lassiipk/ModuPad_v2/Assets/nice!view/Screenshot 2026-01-20 105709.png

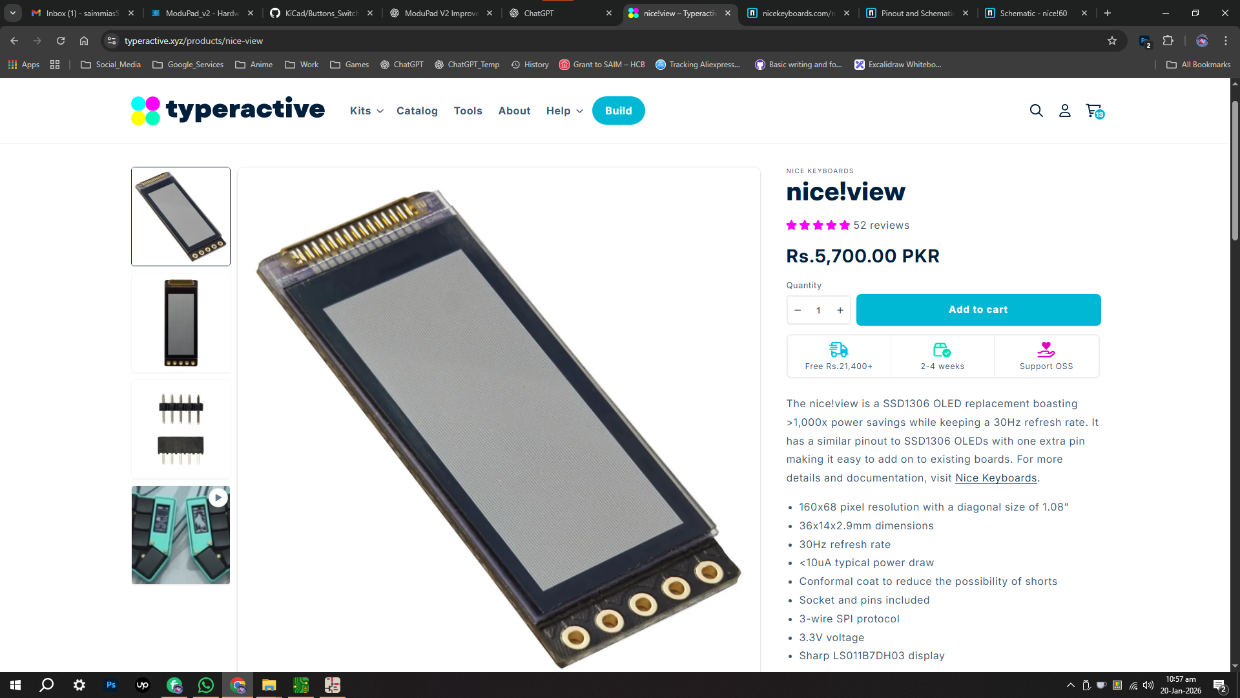
Assets/nice!view/Screenshot 2026-01-20 105709.png
