lassiipk/ModuPad_v2/CAD/Knobs/Knurled Encoder Knob/Knob Back.png

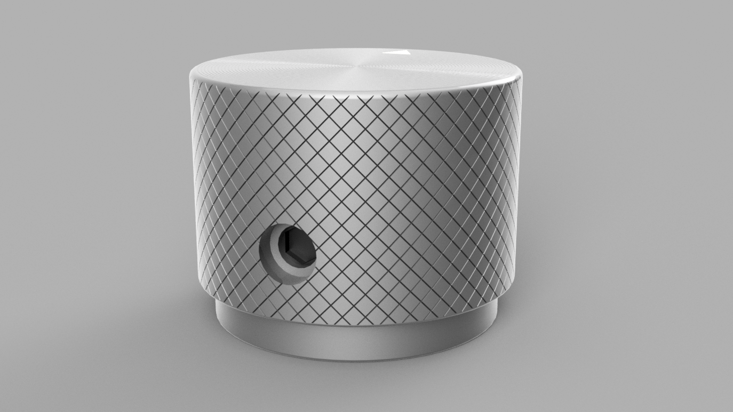
CAD/Knobs/Knurled Encoder Knob/Knob Back.png
