lassiipk/ModuPad_v2/CAD/Knobs/Knurled Encoder Knob/Knob Bottom.png

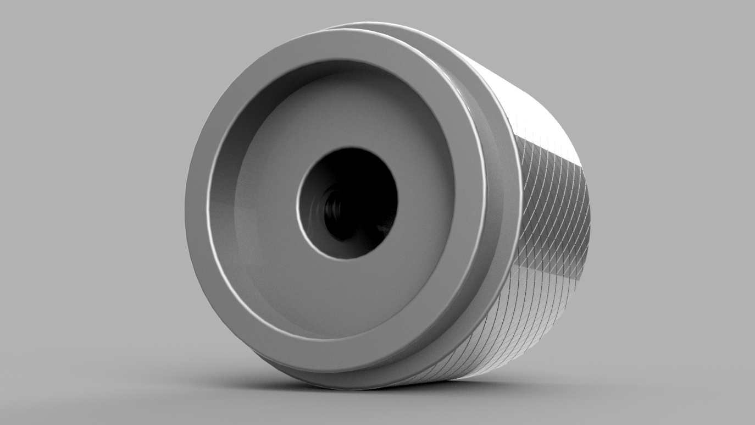
CAD/Knobs/Knurled Encoder Knob/Knob Bottom.png
