lassiipk/ModuPad_v2/CAD/Knobs/Knurled Encoder Knob/Knob Top.png

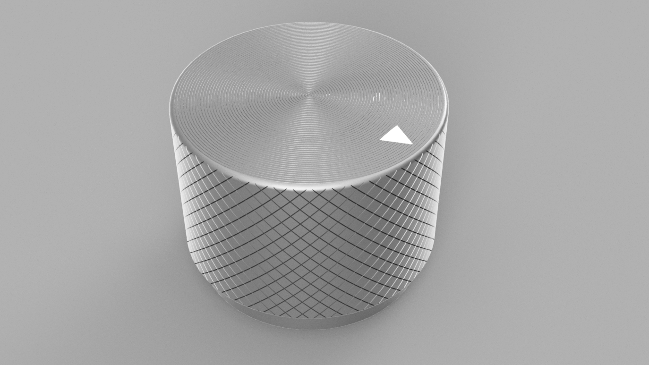
CAD/Knobs/Knurled Encoder Knob/Knob Top.png
