lassiipk/ModuPad_v2/Images/CAD/CAD_Sketch/CAD_Bottom_Sketch_Screenshot 2026-01-29 163341.png

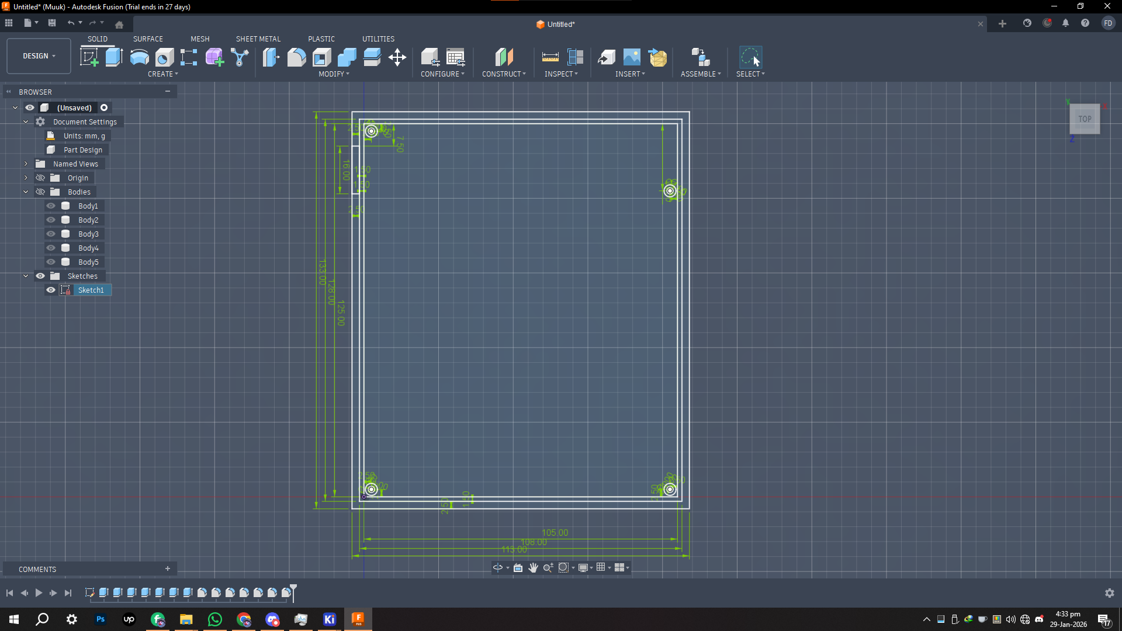
Images/CAD/CAD_Sketch/CAD_Bottom_Sketch_Screenshot 2026-01-29 163341.png
