lassiipk/ModuPad_v2/Images/CAD/CAD_Sketch/Screenshot 2026-01-31 225652.png

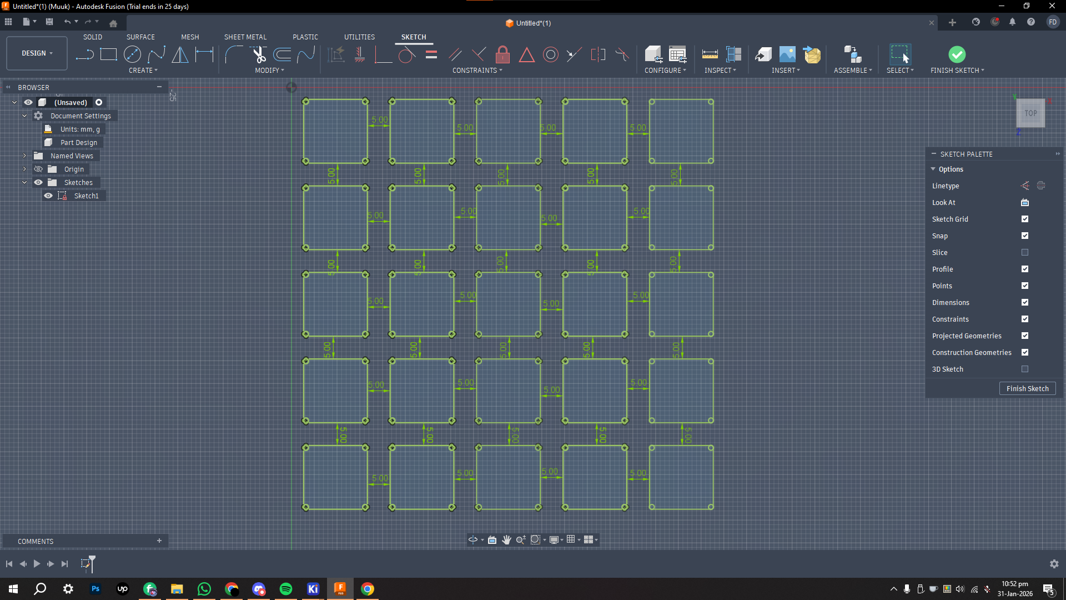
Images/CAD/CAD_Sketch/Screenshot 2026-01-31 225652.png
