lassiipk/ModuPad_v2/Images/CAD/CAD_Sketch/Screenshot 2026-01-31 235744.png

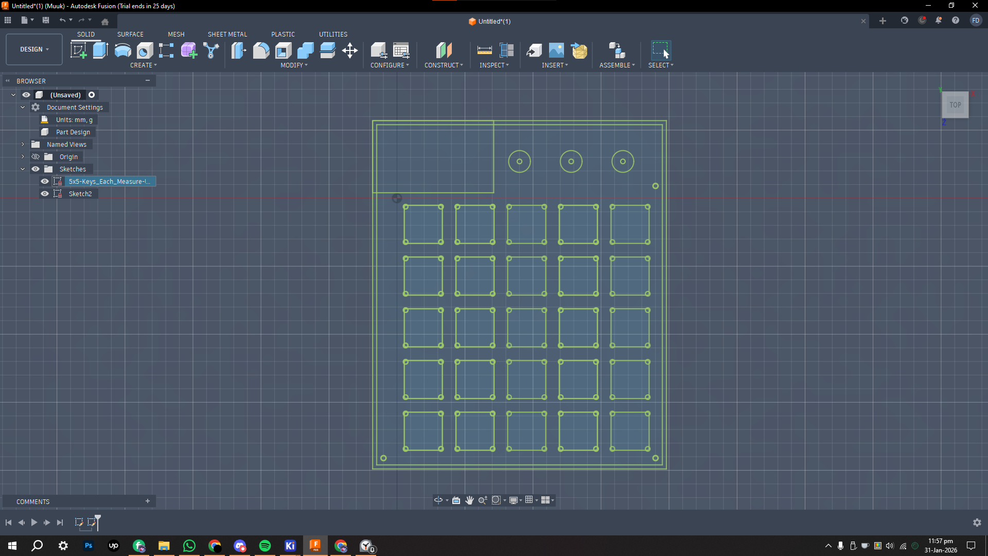
Images/CAD/CAD_Sketch/Screenshot 2026-01-31 235744.png
