lassiipk/ModuPad_v2/Images/CAD/CAD_Sketch/Screenshot 2026-02-04 113914.png

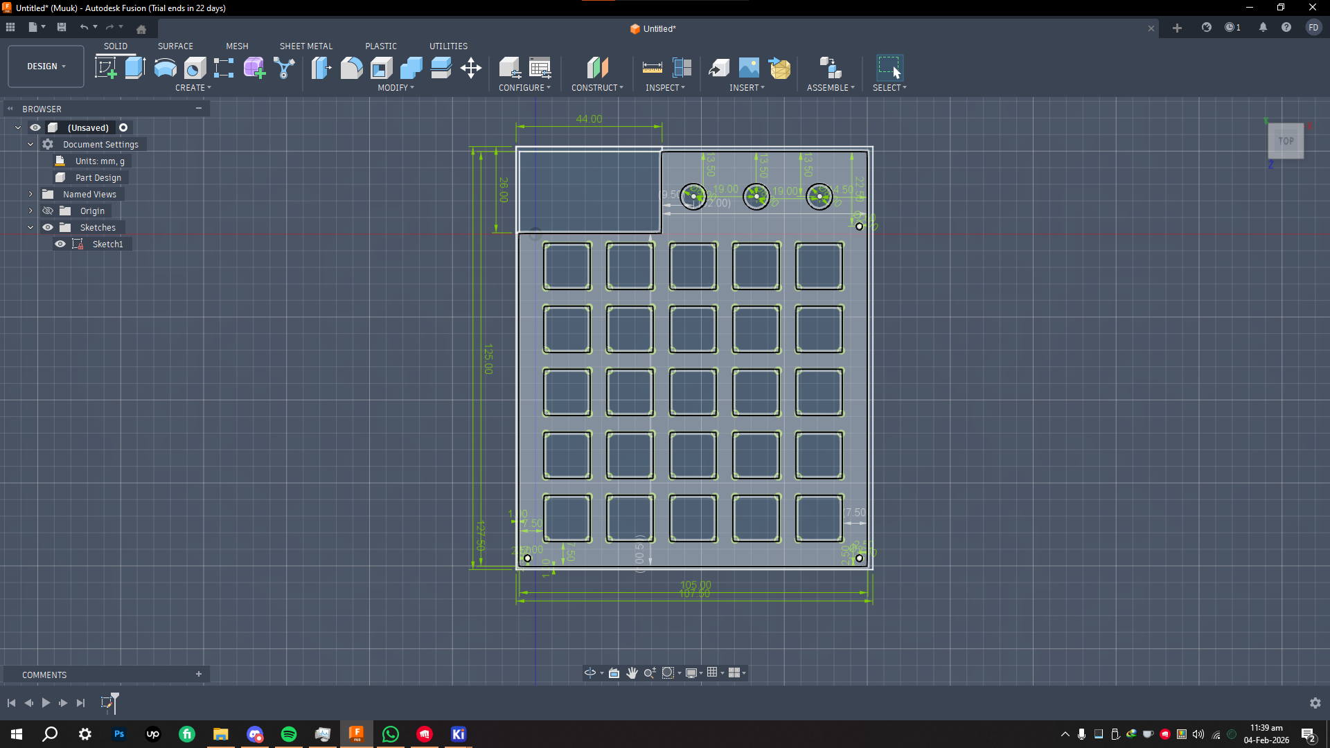
Images/CAD/CAD_Sketch/Screenshot 2026-02-04 113914.png
