lassiipk/ModuPad_v2/Images/CAD/CAD_Solid/CAD_Bottom_Solid_2.o_Screenshot 2026-01-29 163546.png

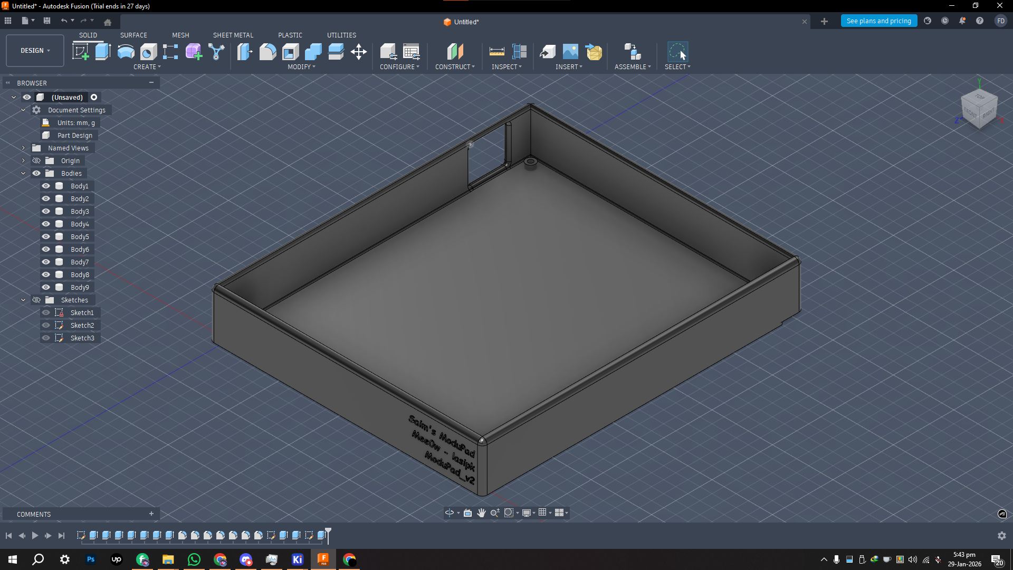
Images/CAD/CAD_Solid/CAD_Bottom_Solid_2.o_Screenshot 2026-01-29 163546.png
