lassiipk/ModuPad_v2/Images/PCB/Screenshot 2026-01-23 115402.png

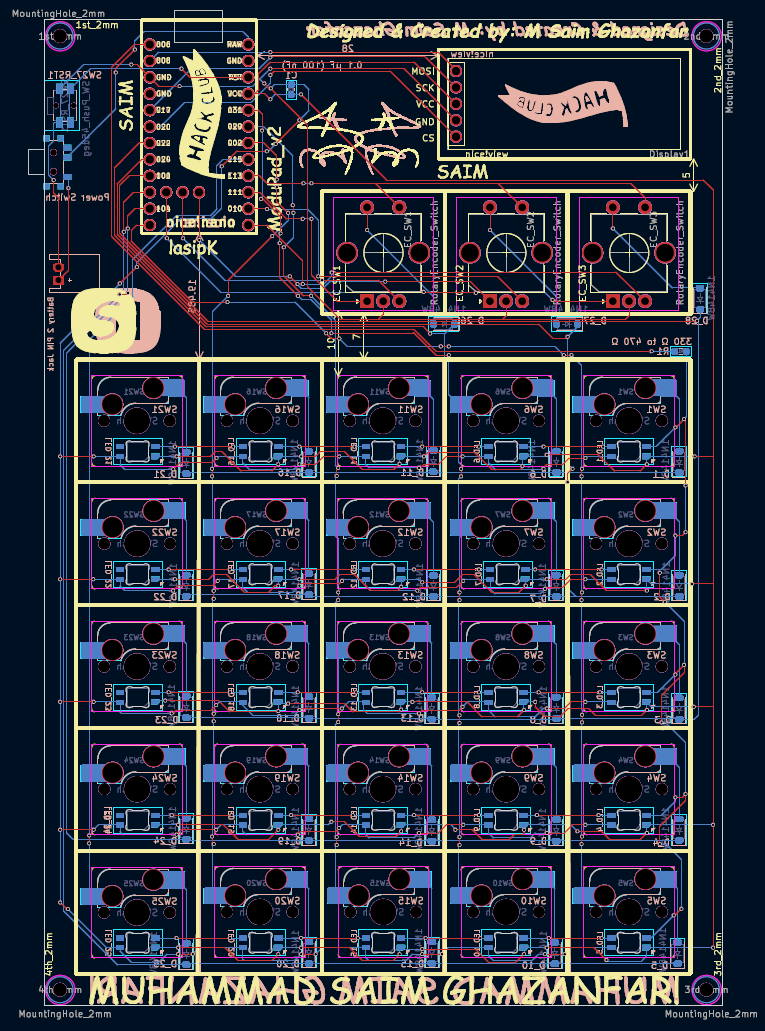
Images/PCB/Screenshot 2026-01-23 115402.png
