lassiipk/ModuPad_v2/Images/PCB/Screenshot 2026-01-26 182227.png

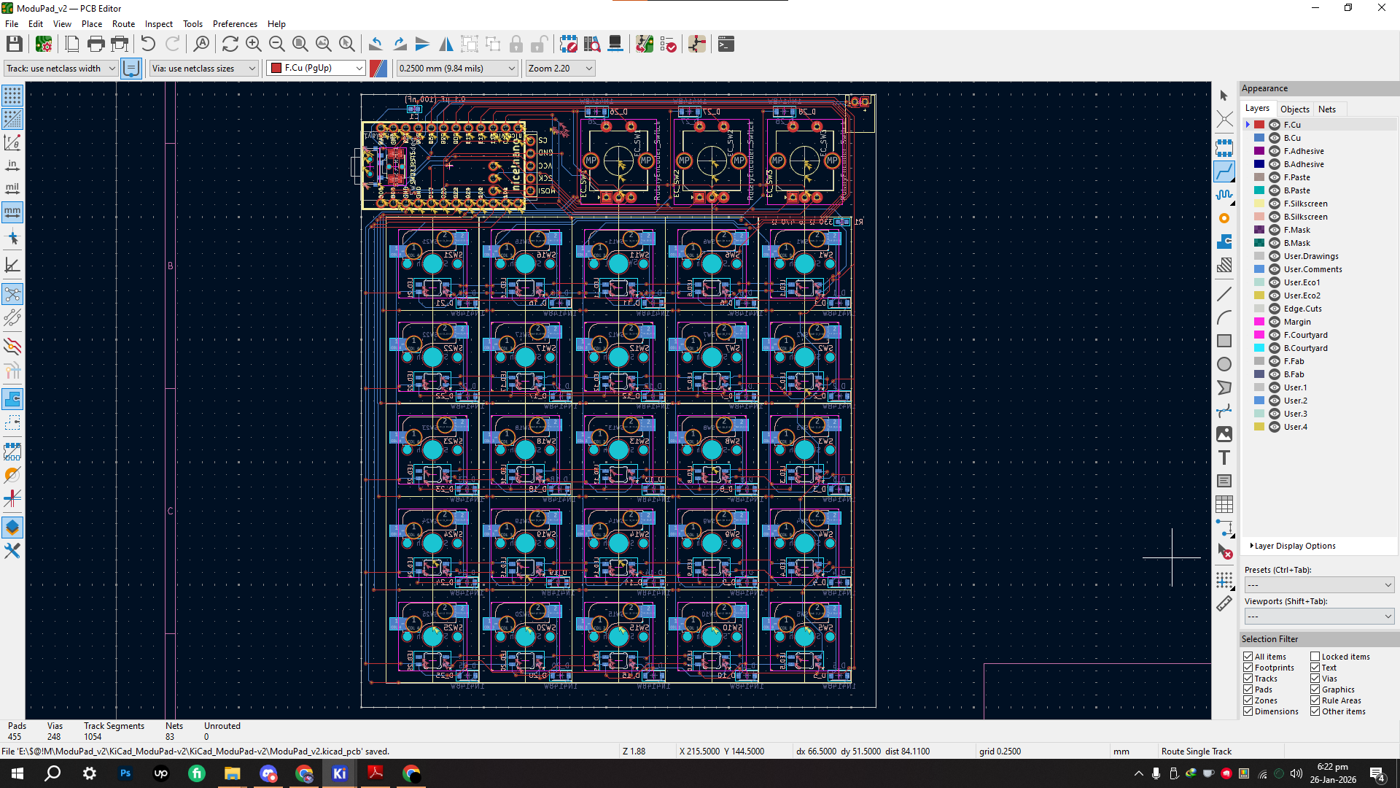
Images/PCB/Screenshot 2026-01-26 182227.png
