lassiipk/ModuPad_v2/Images/PCB/Screenshot 2026-01-27 120922.png

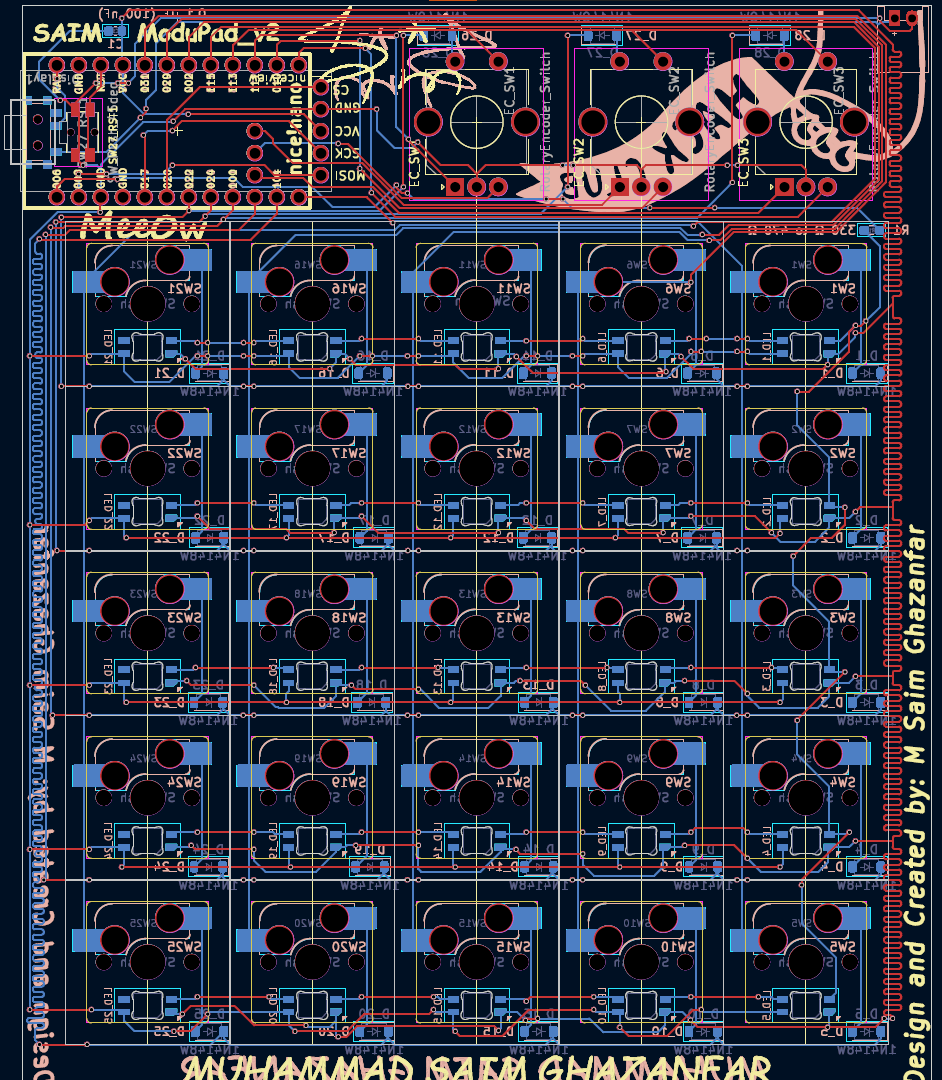
Images/PCB/Screenshot 2026-01-27 120922.png
