lassiipk/ModuPad_v2/Images/PCB/Screenshot 2026-03-08 180335.png

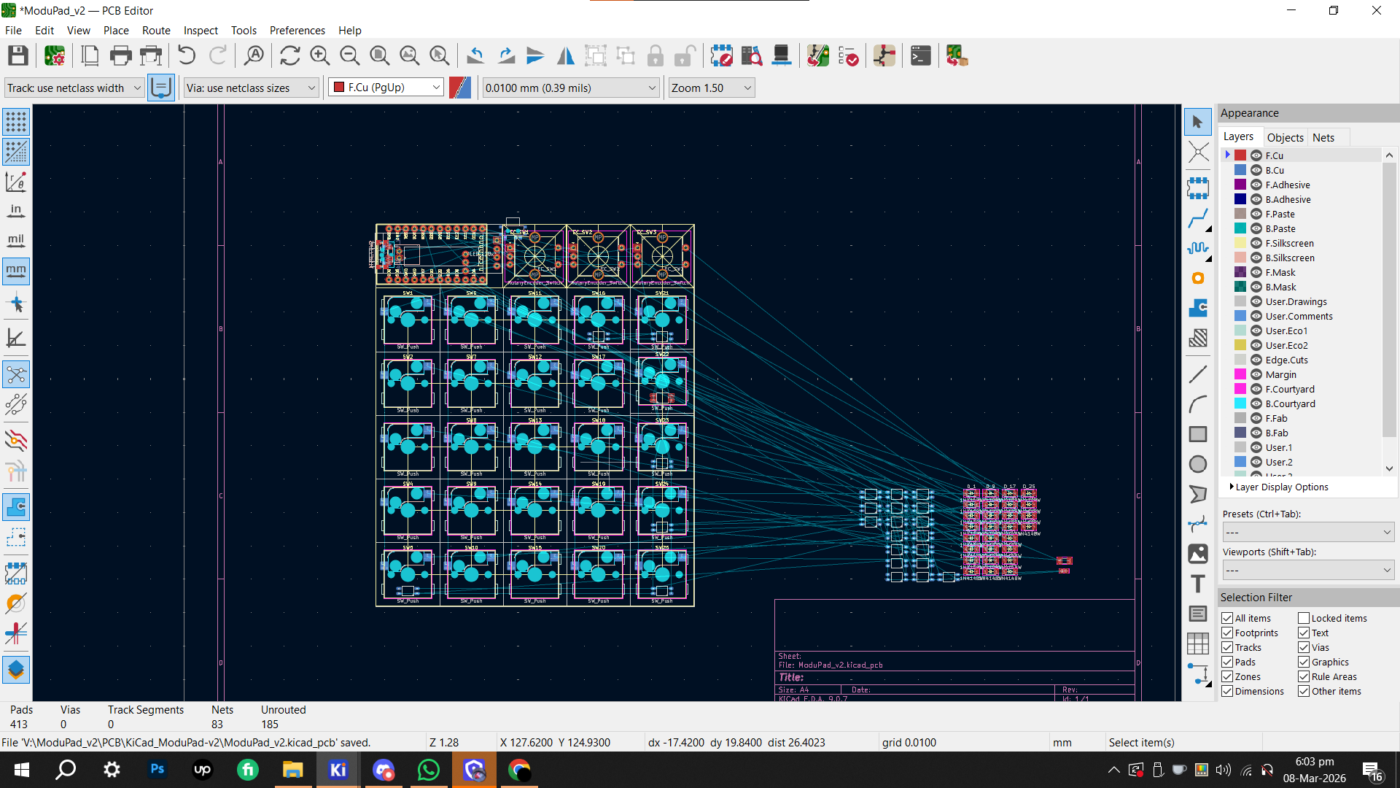
Images/PCB/Screenshot 2026-03-08 180335.png
