lassiipk/ModuPad_v2/Images/PCB/Screenshot 2026-03-09 xxxxxx.png

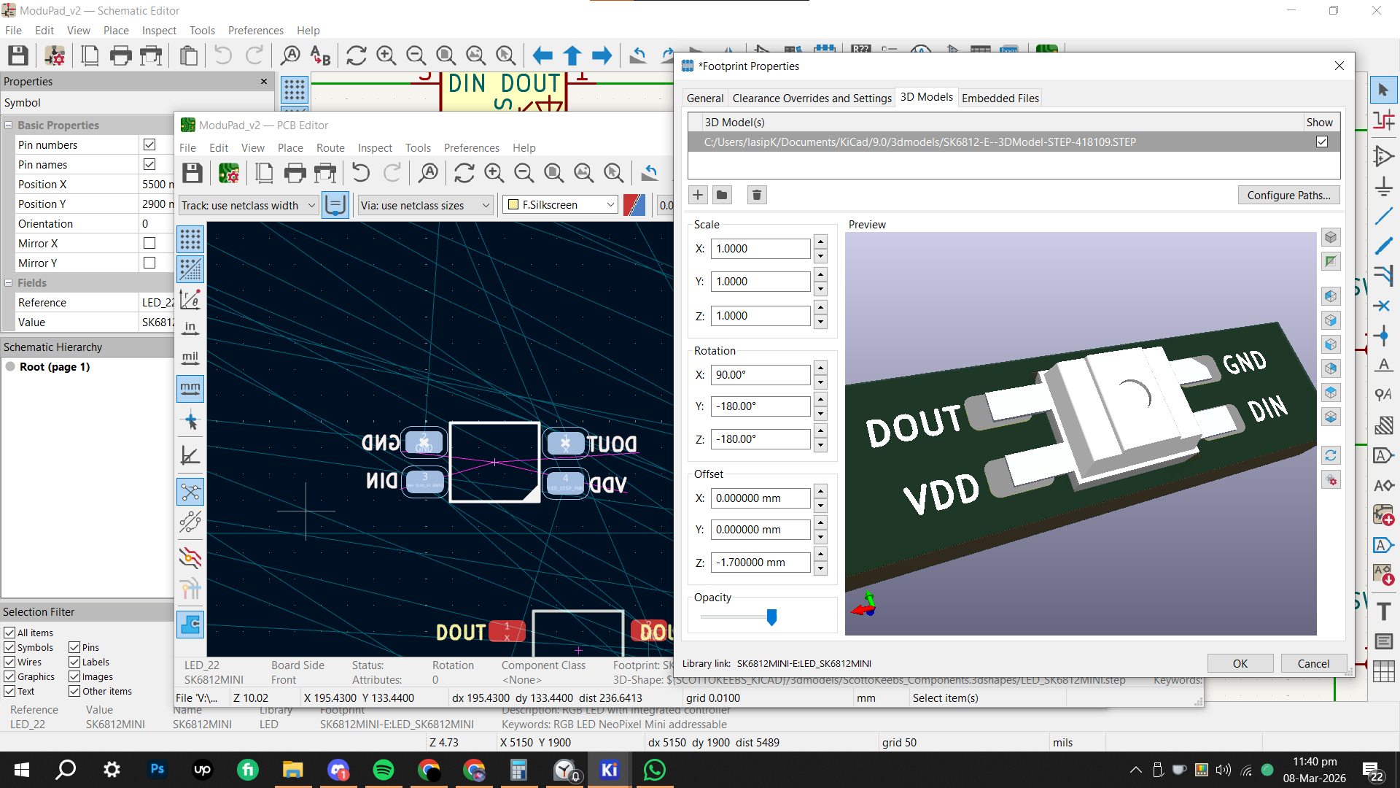
Images/PCB/Screenshot 2026-03-09 xxxxxx.png
