lassiipk/ModuPad_v2/Images/PCB/Screenshot 2026-03-10 152446.png

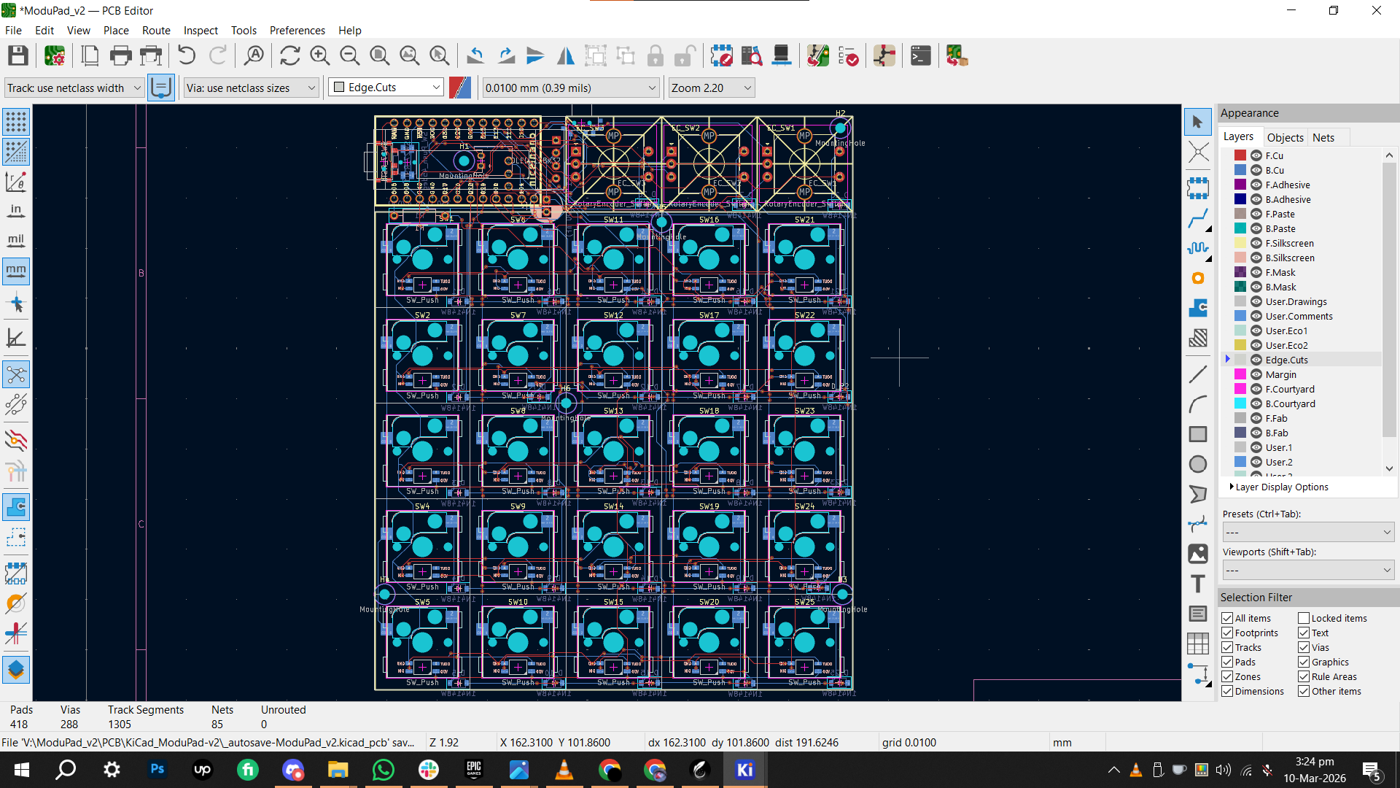
Images/PCB/Screenshot 2026-03-10 152446.png
