lassiipk/ModuPad_v2/Images/PCB/Screenshot 2026-03-20 000157.png

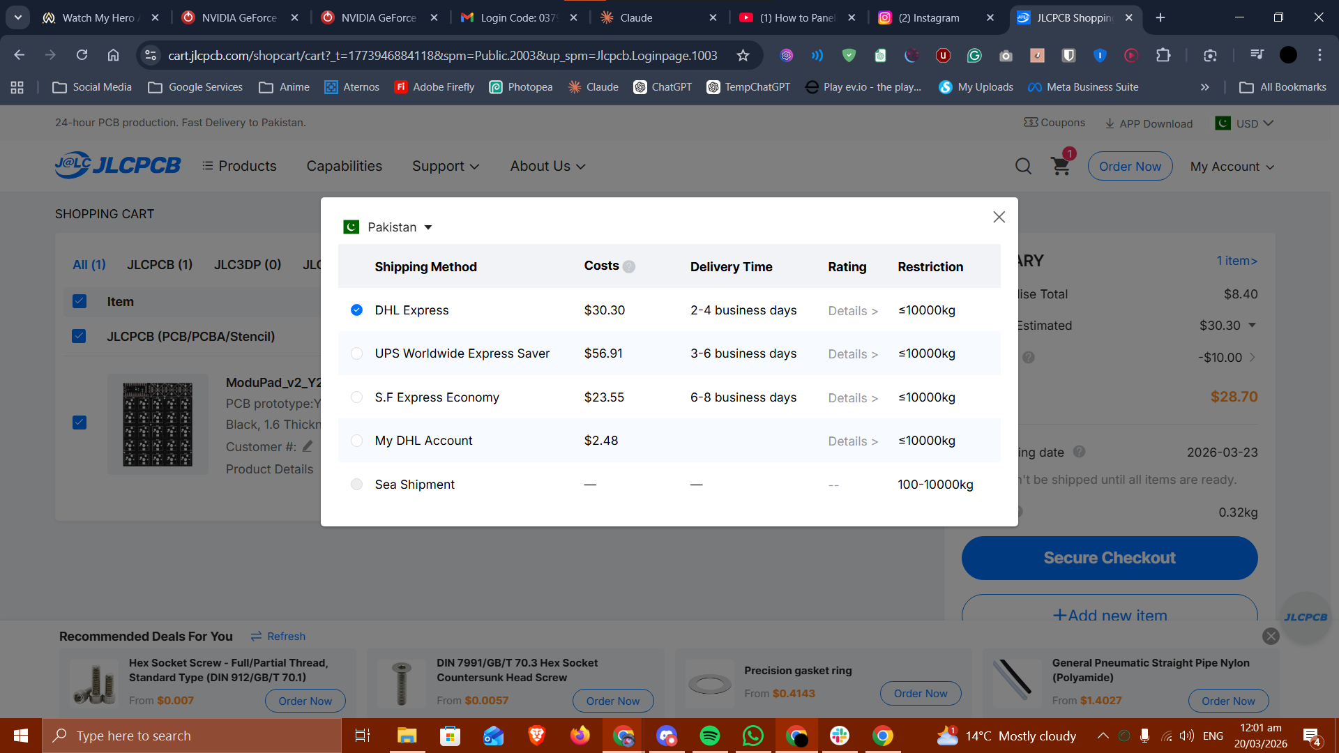
Images/PCB/Screenshot 2026-03-20 000157.png
