lassiipk/ModuPad_v2/Images/Schematic/Screenshot 2026-01-20 235038.png

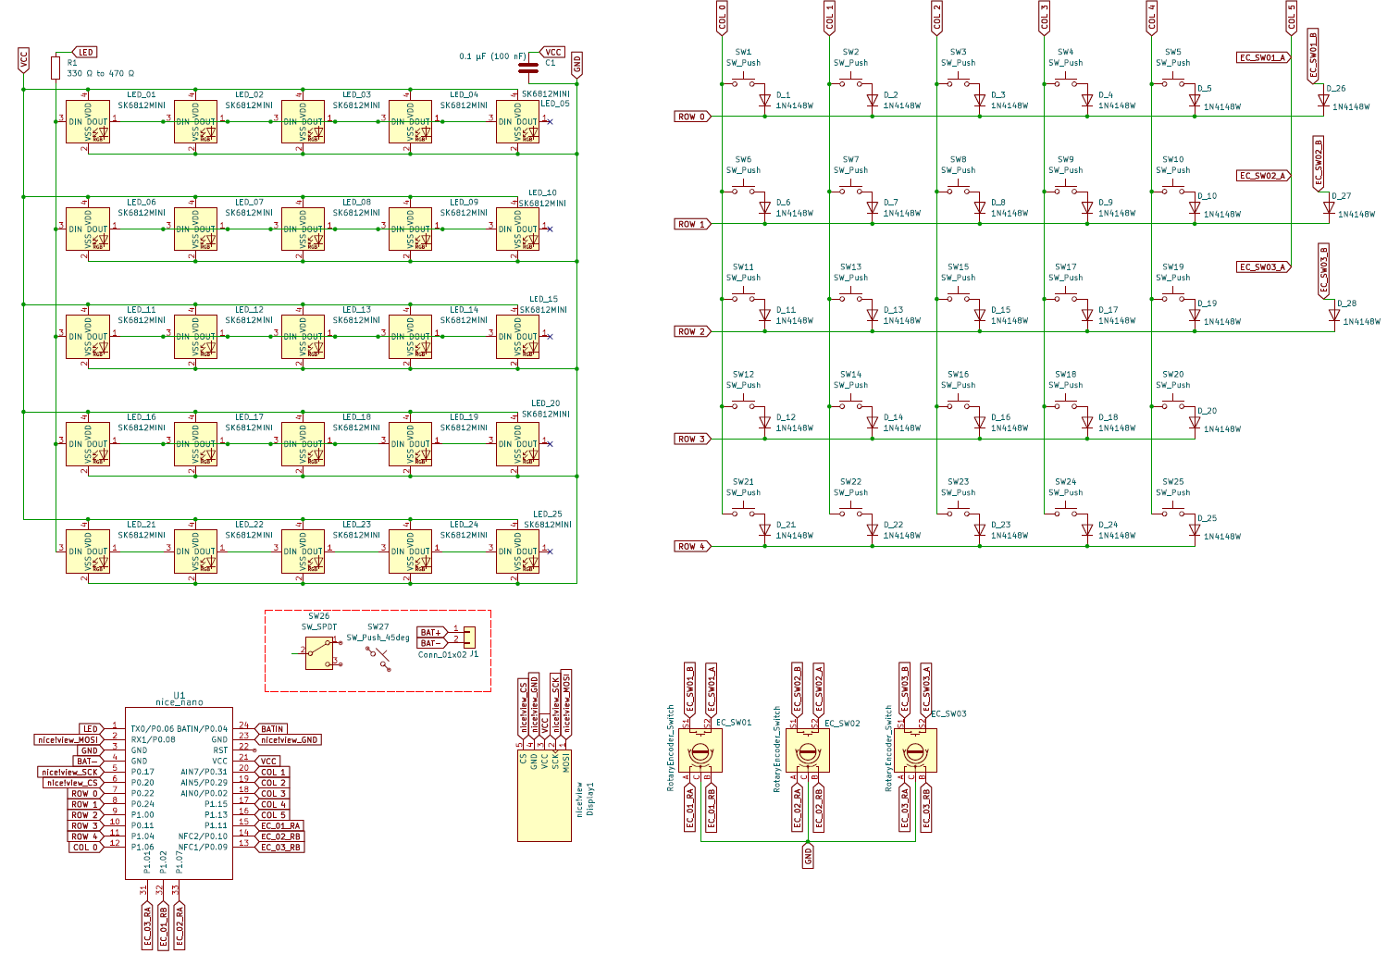
Images/Schematic/Screenshot 2026-01-20 235038.png
