lassiipk/ModuPad_v2/Images/Schematic/Screenshot 2026-03-07 010522.png

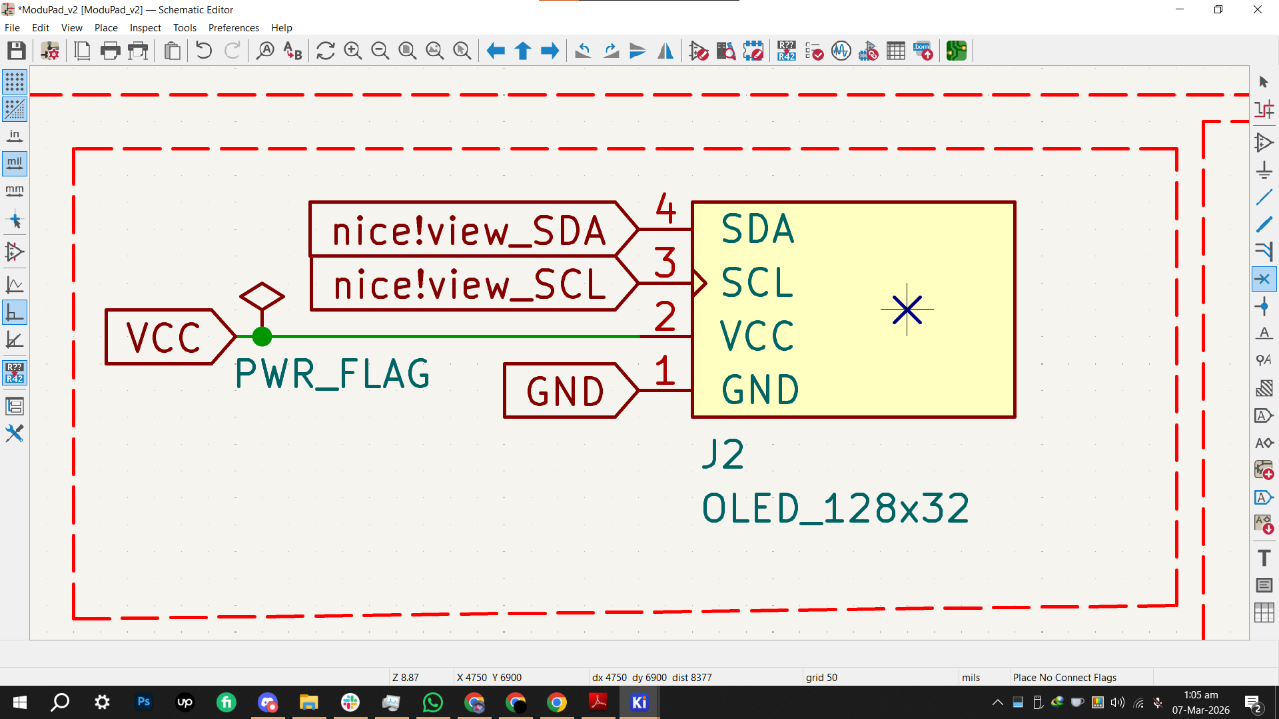
Images/Schematic/Screenshot 2026-03-07 010522.png
