lassiipk/ModuPad_v2/Images/Schematic/Screenshot 2026-03-07 010559.png

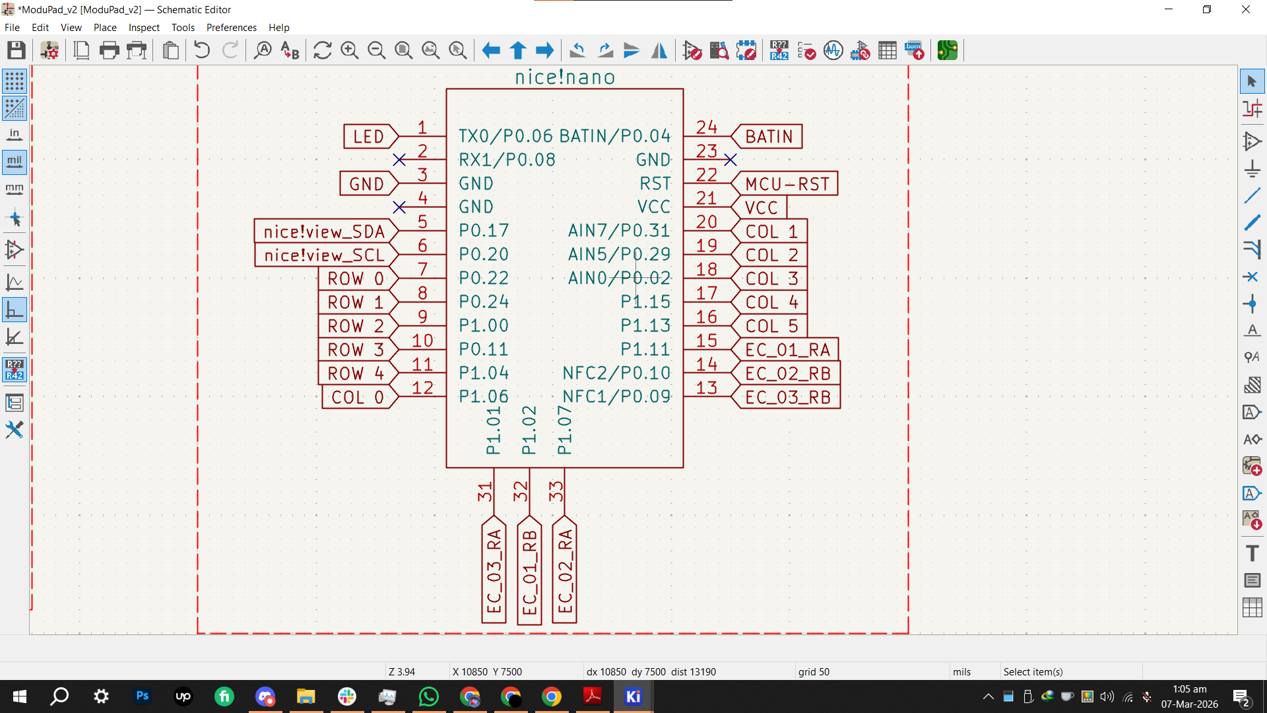
Images/Schematic/Screenshot 2026-03-07 010559.png
