lassiipk/ModuPad_v2/Renders/CAD/CAD_Rendered/Full-CAD/Complete-CAD_2026-Feb-14_11-45-22AM-000_CustomizedView27695672821_png.png

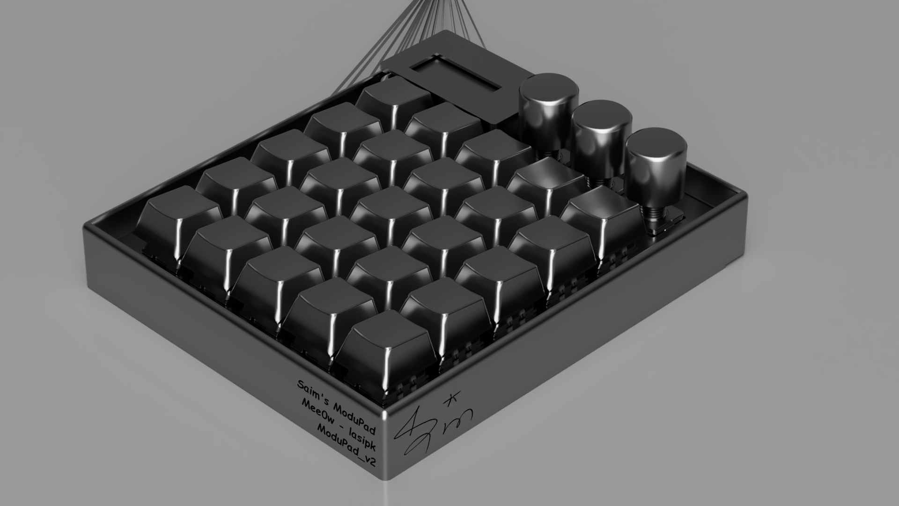
Renders/CAD/CAD_Rendered/Full-CAD/Complete-CAD_2026-Feb-14_11-45-22AM-000_CustomizedView27695672821_png.png
