lassiipk/ModuPad_v2/Renders/KiCad/Compiling/ModuPad_v2_Front-Side_2.o.png

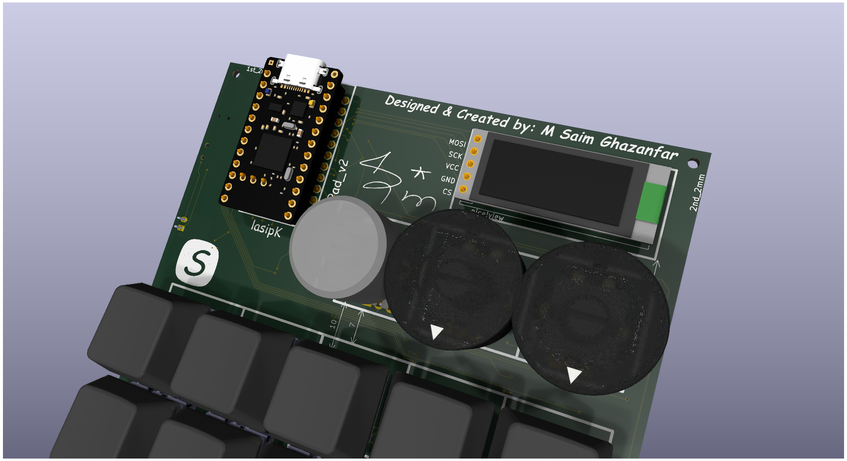
Renders/KiCad/Compiling/ModuPad_v2_Front-Side_2.o.png
