lassiipk/ModuPad_v2/Renders/KiCad/Compiling/Screenshot 2026-01-21 223556.png

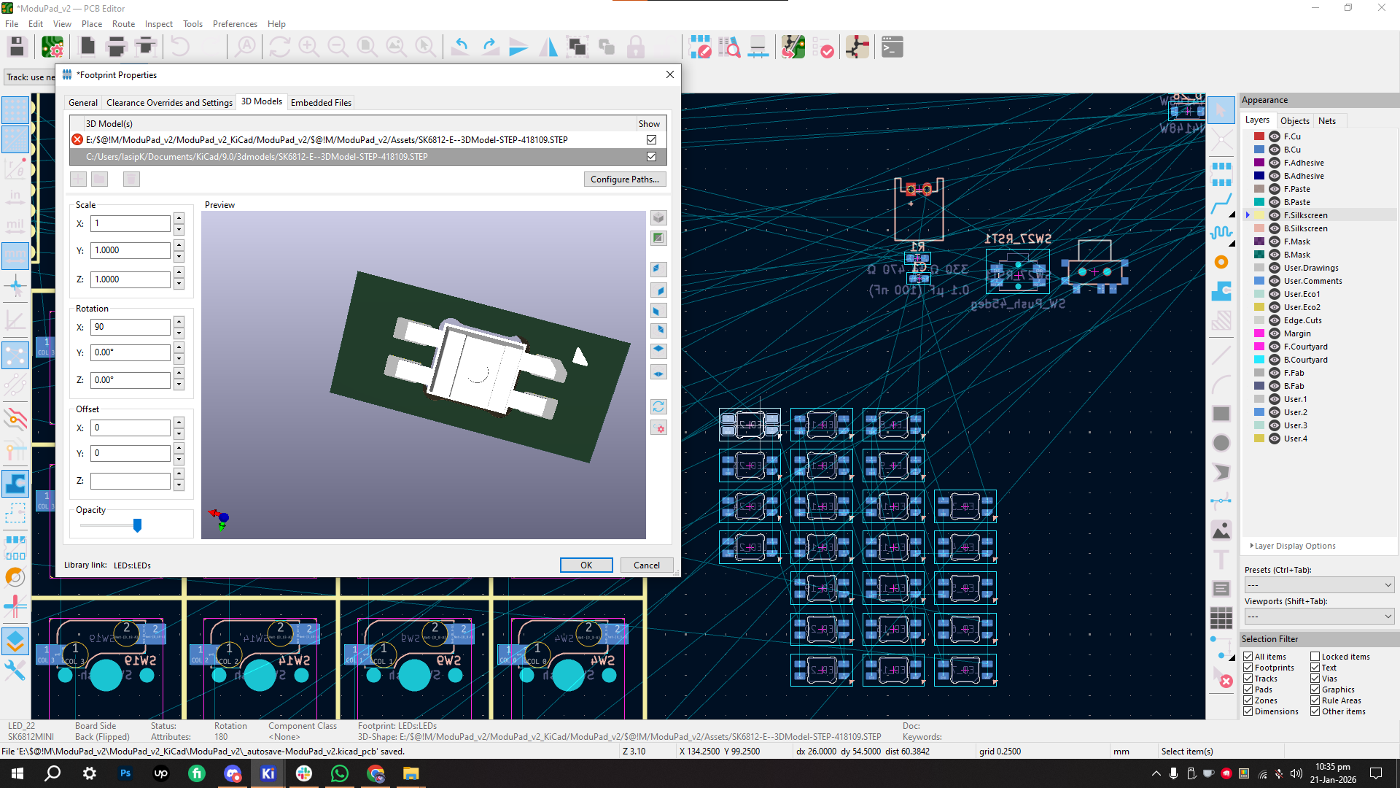
Renders/KiCad/Compiling/Screenshot 2026-01-21 223556.png
