lassiipk/ModuPad_v2/Renders/KiCad/Compiling/Screenshot 2026-01-22 001031.png

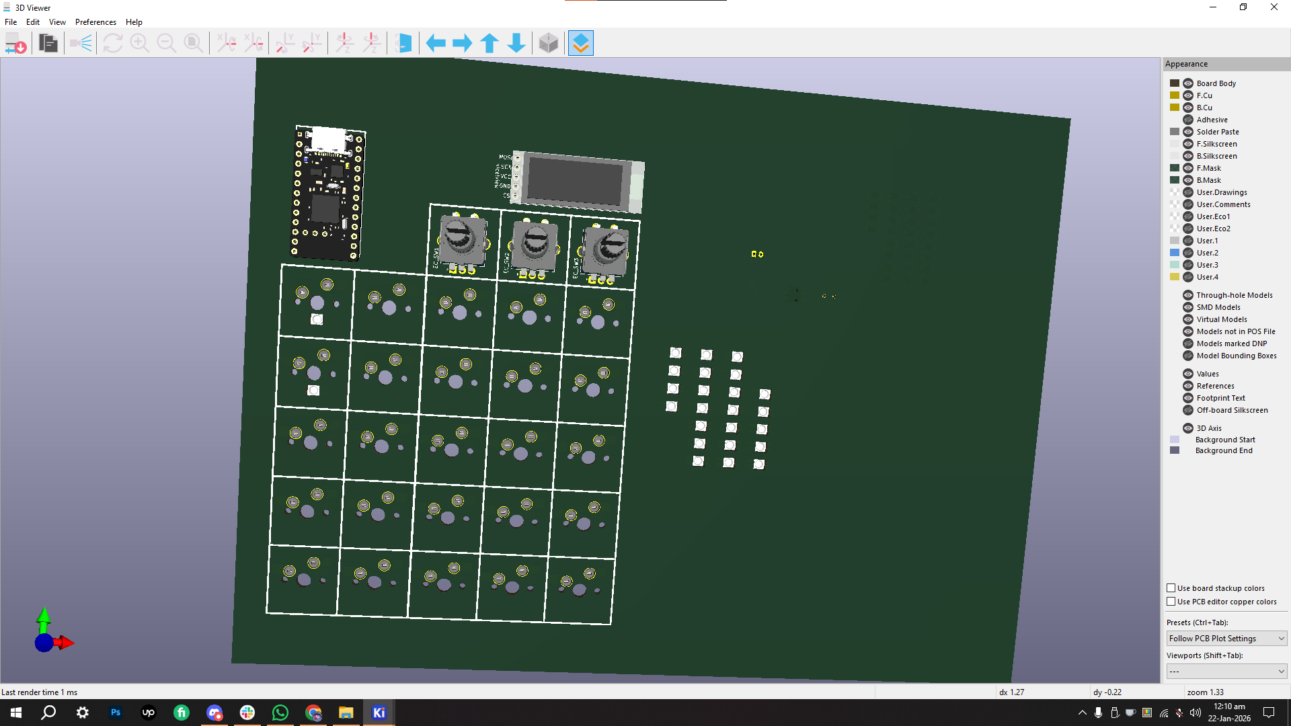
Renders/KiCad/Compiling/Screenshot 2026-01-22 001031.png
