lassiipk/ModuPad_v2/Renders/KiCad/Compiling/Screenshot 2026-01-22 010454.png

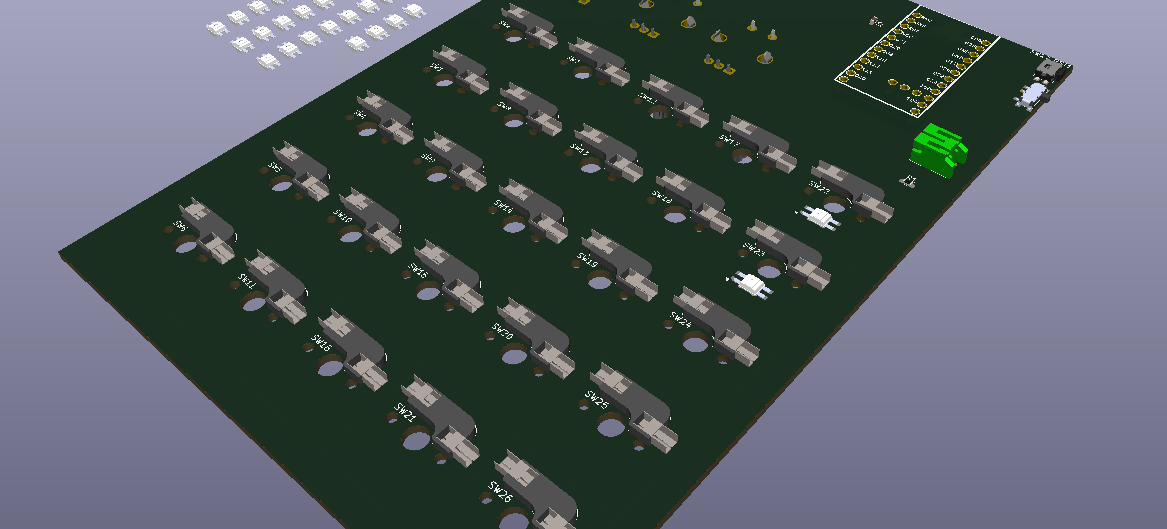
Renders/KiCad/Compiling/Screenshot 2026-01-22 010454.png
