lassiipk/ModuPad_v2/Renders/KiCad/ModuPad_v2_Design_1.o/ModuPad_v2_Front-Side.png

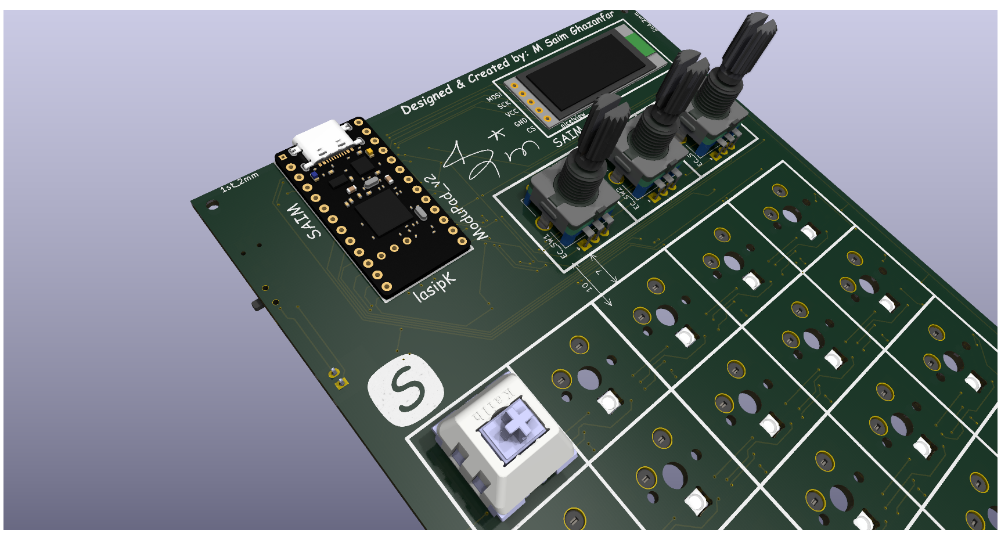
Renders/KiCad/ModuPad_v2_Design_1.o/ModuPad_v2_Front-Side.png
