lassiipk/ModuPad_v2/Renders/KiCad/ModuPad_v2_Design_2.o/ModuPad_v2_nice!view-AND-nicenano_2.o.png

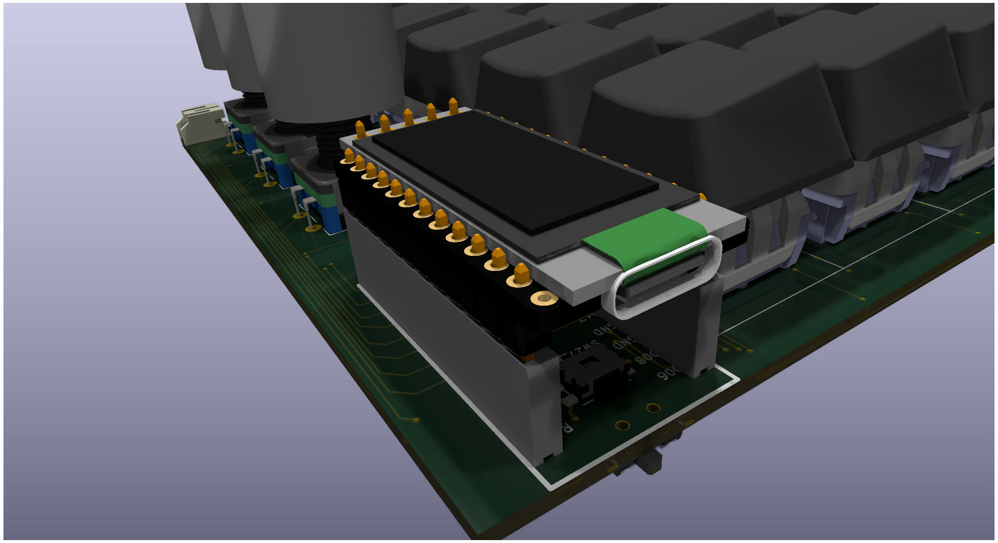
Renders/KiCad/ModuPad_v2_Design_2.o/ModuPad_v2_nice!view-AND-nicenano_2.o.png
