lassiipk/ModuPad_v2/BOM/Cart_Images/Aliexpress_Screenshot 2026-02-17 111641.png

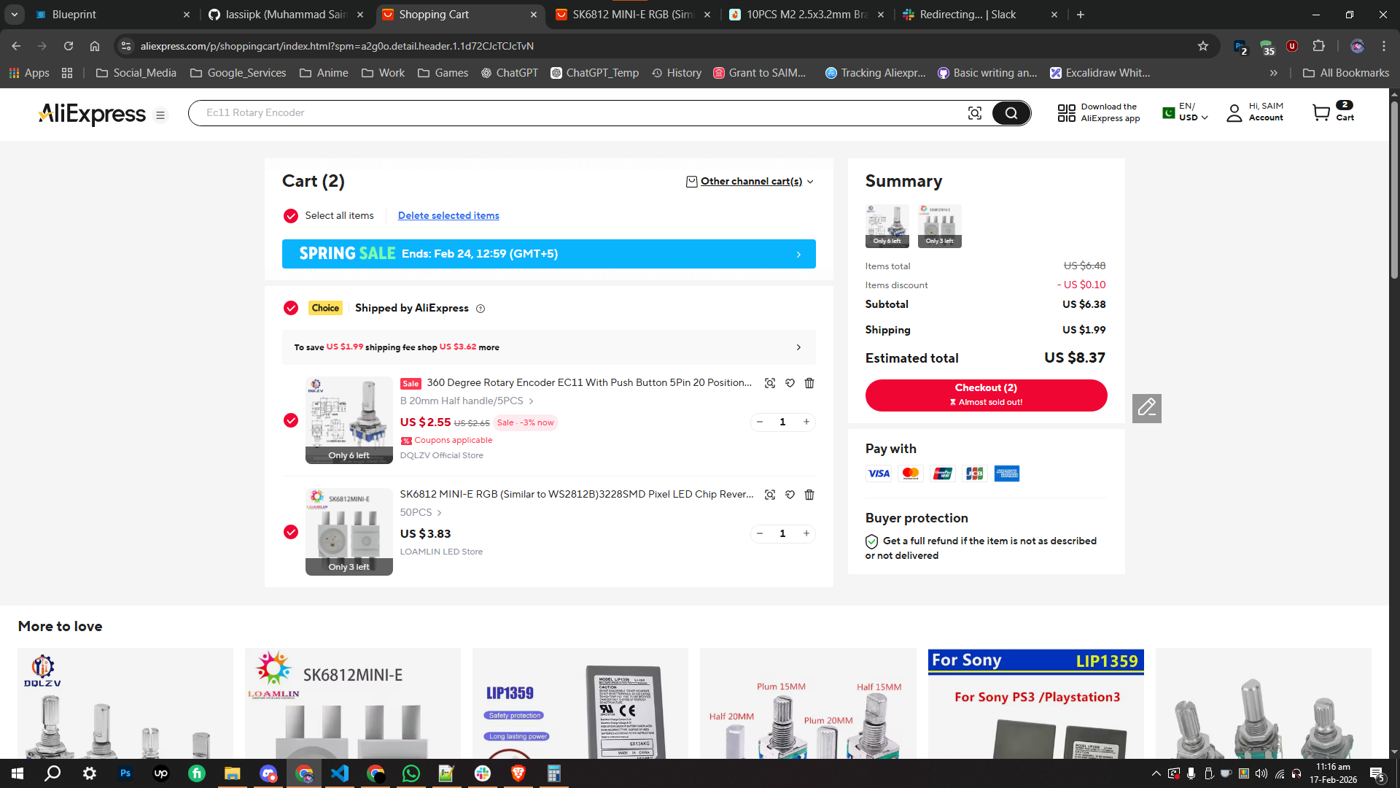
BOM/Cart_Images/Aliexpress_Screenshot 2026-02-17 111641.png
