lassiipk/ModuPad_v2/BOM/Cart_Images/AliExpress_Screenshot-2026-03-10-170552.png

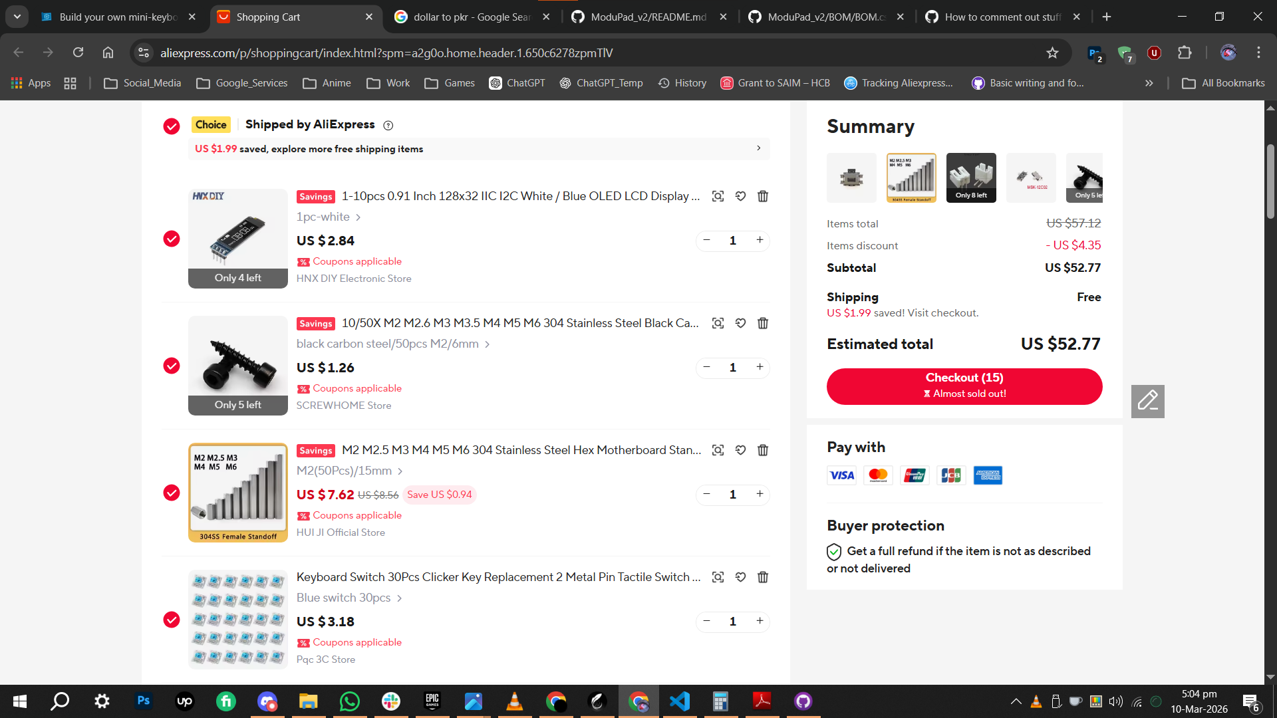
BOM/Cart_Images/AliExpress_Screenshot-2026-03-10-170552.png
