lassiipk/ModuPad_v2/BOM/Cart_Images/Daraz_Screenshot 2026-02-17 112123.png

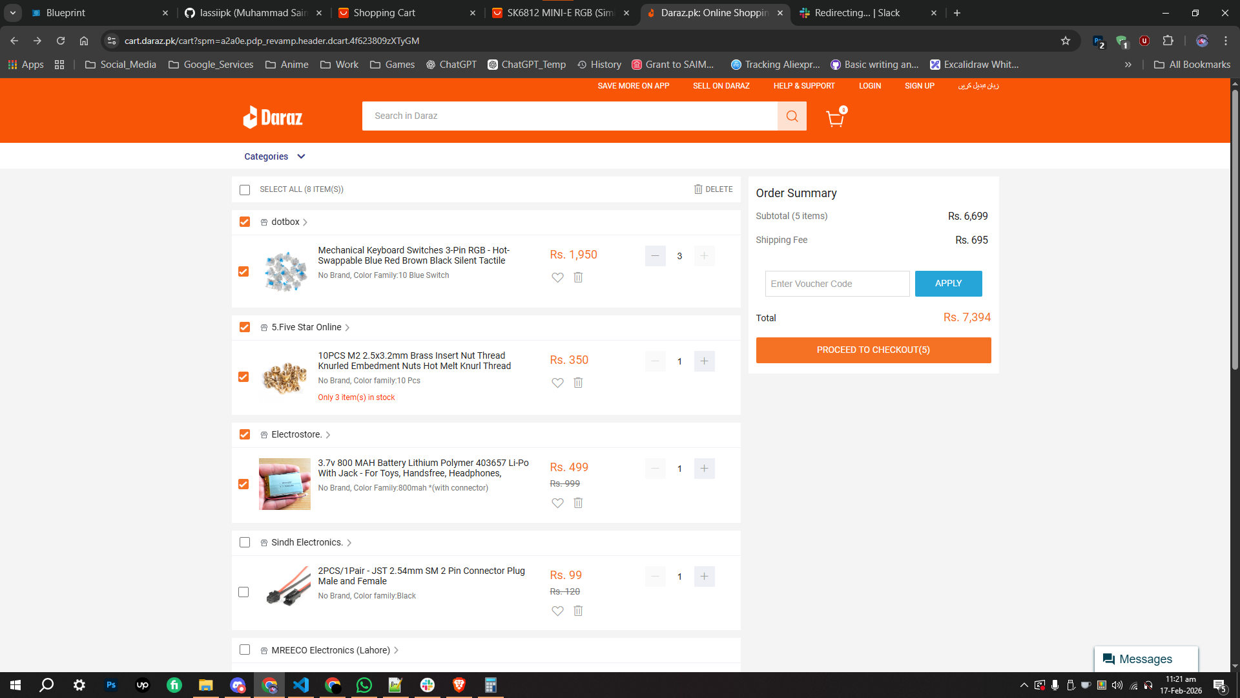
BOM/Cart_Images/Daraz_Screenshot 2026-02-17 112123.png
