lassiipk/ModuPad_v2/BOM/Cart_Images/JLCPCB_Screenshot 2026-02-17 172243.png

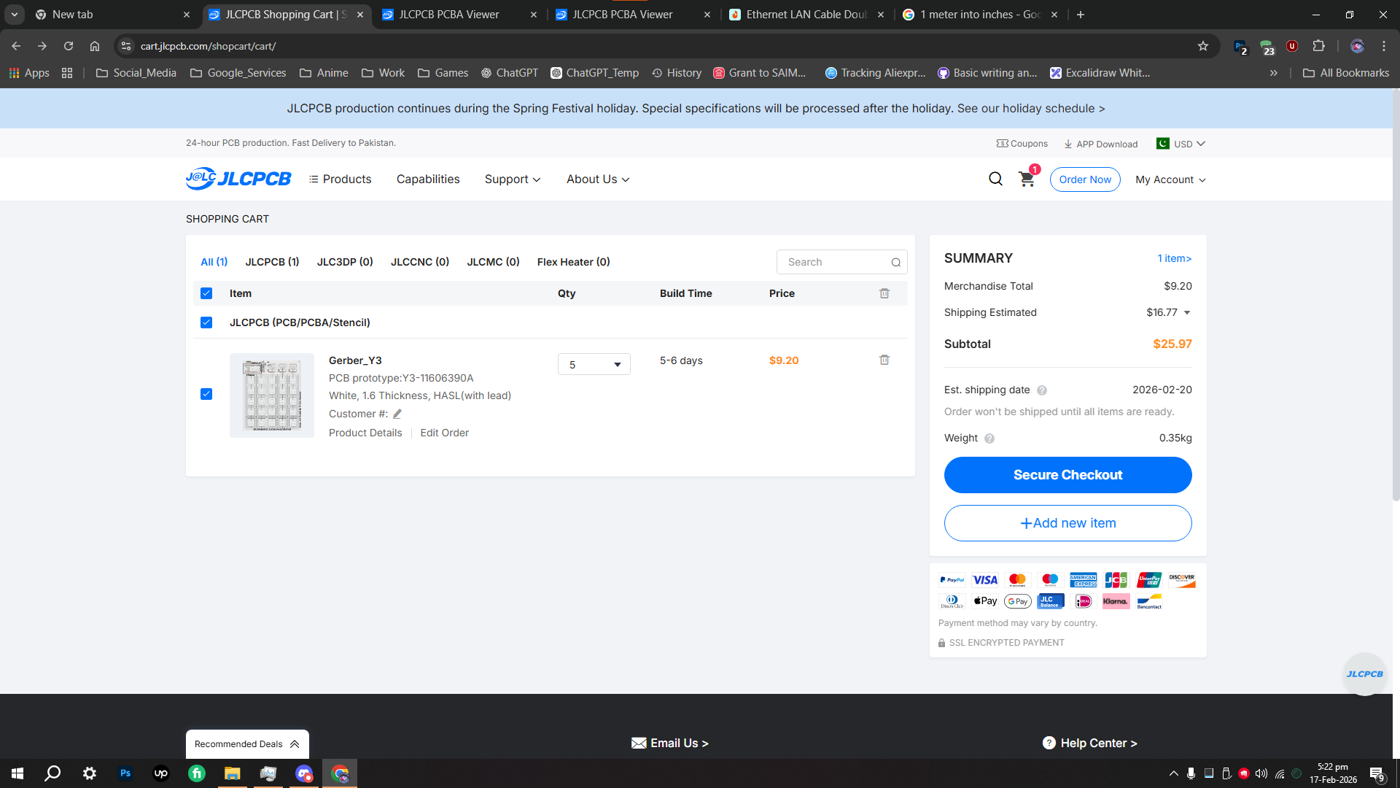
BOM/Cart_Images/JLCPCB_Screenshot 2026-02-17 172243.png
