lassiipk/ModuPad_v2/BOM/Cart_Images/JLCPCB_Screenshot-2026-03-17-183200.png

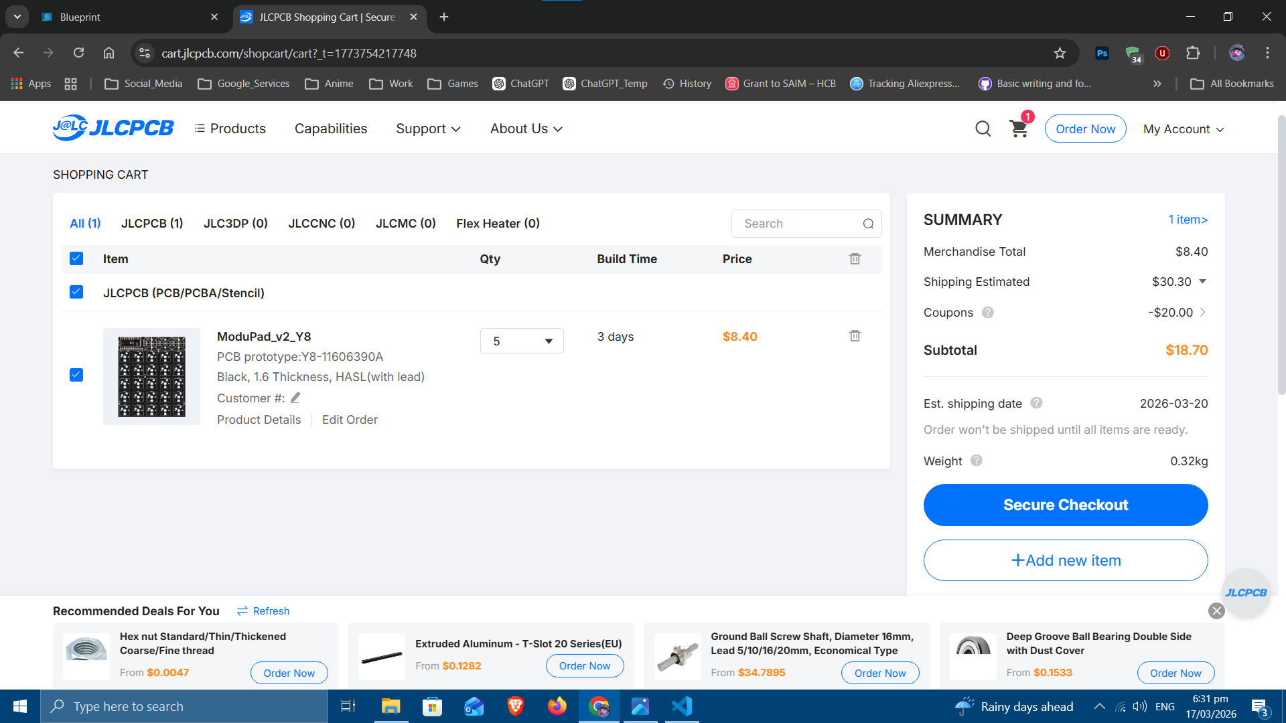
BOM/Cart_Images/JLCPCB_Screenshot-2026-03-17-183200.png
