lassiipk/ModuPad_v2/BOM/Cart_Images/Typeractive_Cart-02_Screenshot 2026-02-17 112352.png

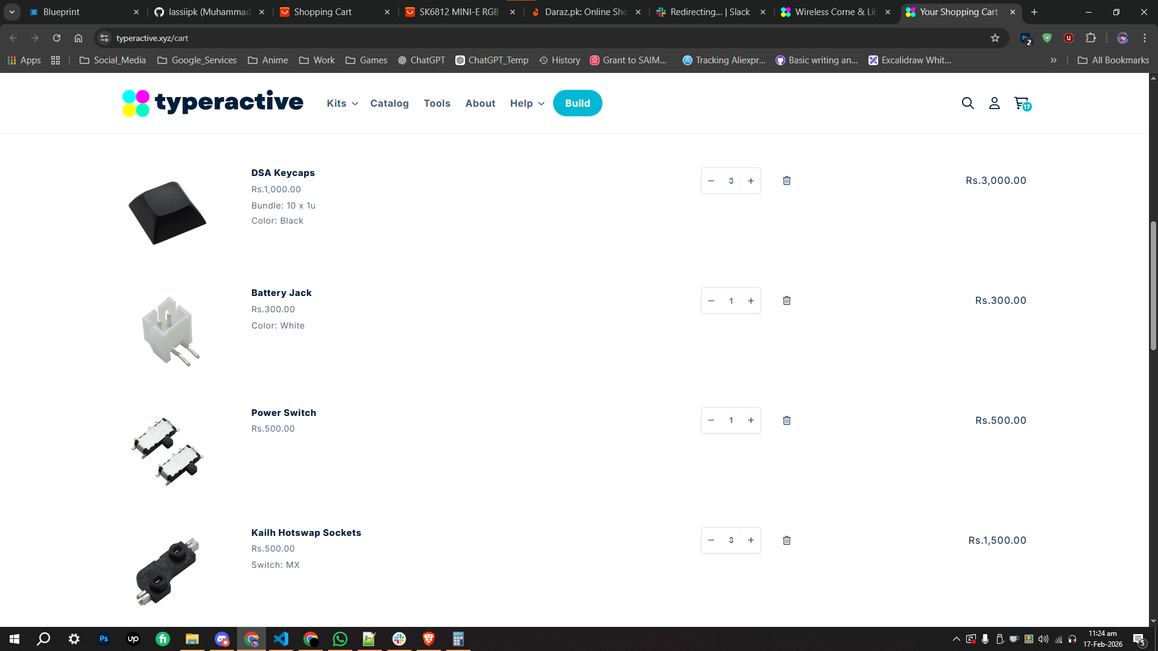
BOM/Cart_Images/Typeractive_Cart-02_Screenshot 2026-02-17 112352.png
