lassiipk/ModuPad_v2/Images/BOM/Screenshot 2026-02-17 202018.png

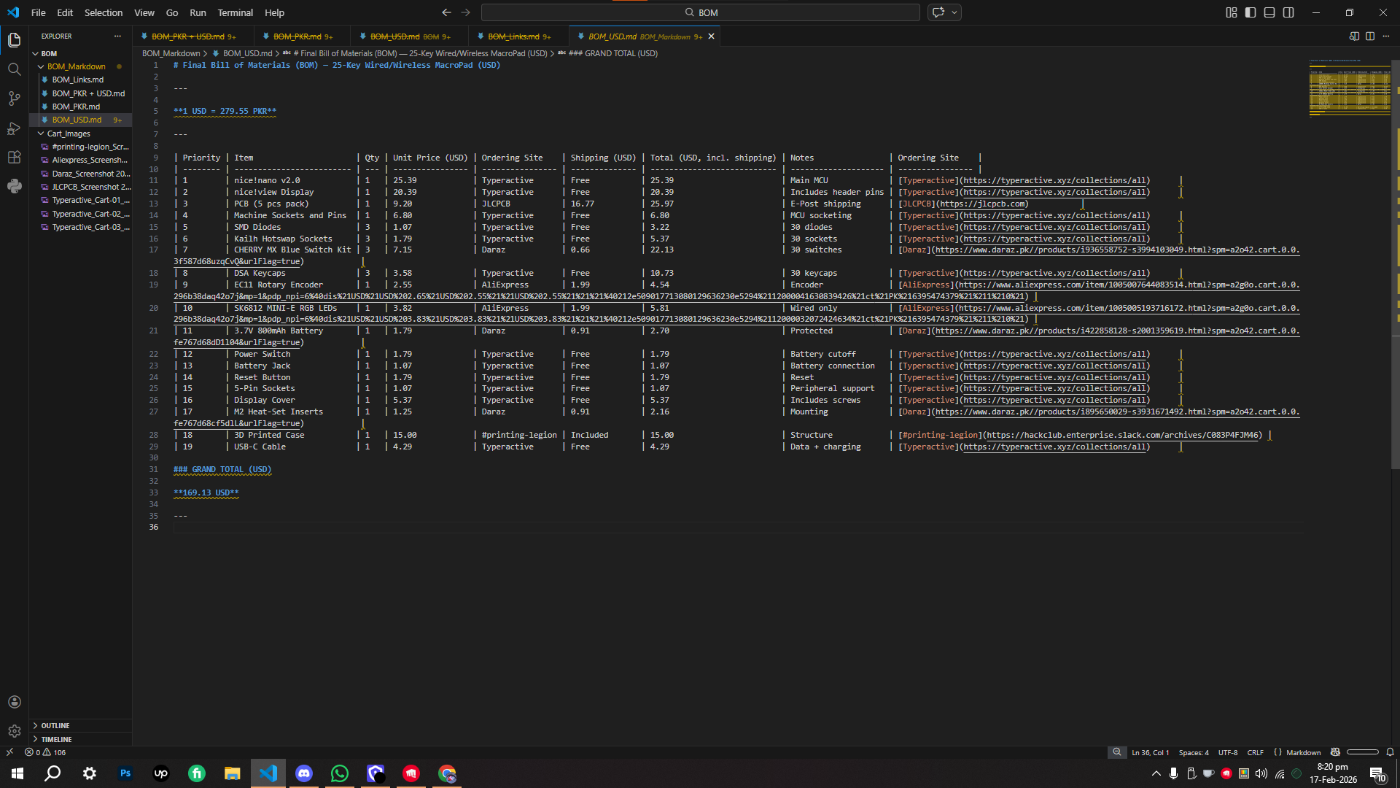
Images/BOM/Screenshot 2026-02-17 202018.png
