lassiipk/ModuPad_v2/Images/BOM/Screenshot 2026-02-27 040207.png

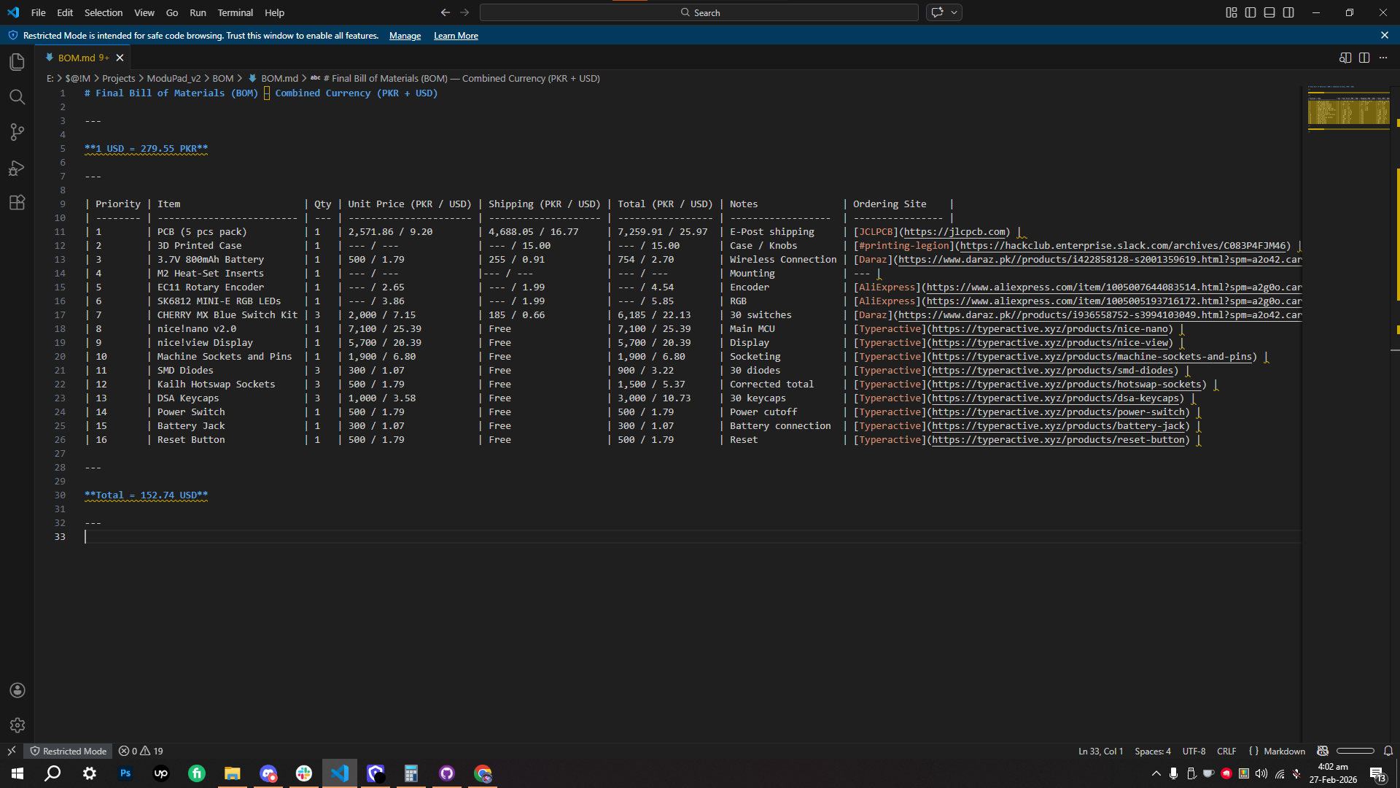
Images/BOM/Screenshot 2026-02-27 040207.png
