lassiipk/ModuPad_v2/Images/BOM/Screenshot 2026-03-10 164351.png

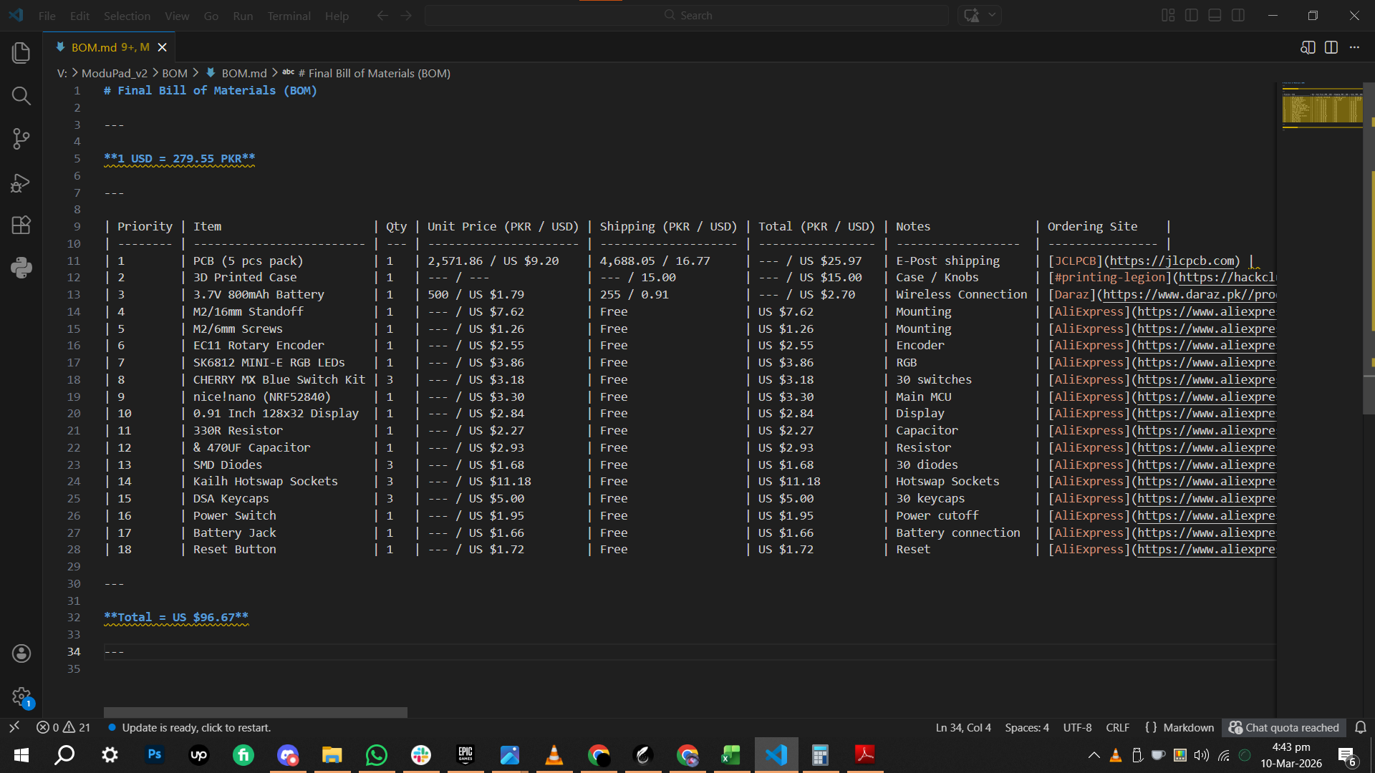
Images/BOM/Screenshot 2026-03-10 164351.png
