lassiipk/ModuPad_v2/Images/BOM/Screenshot 2026-03-10 170257.png

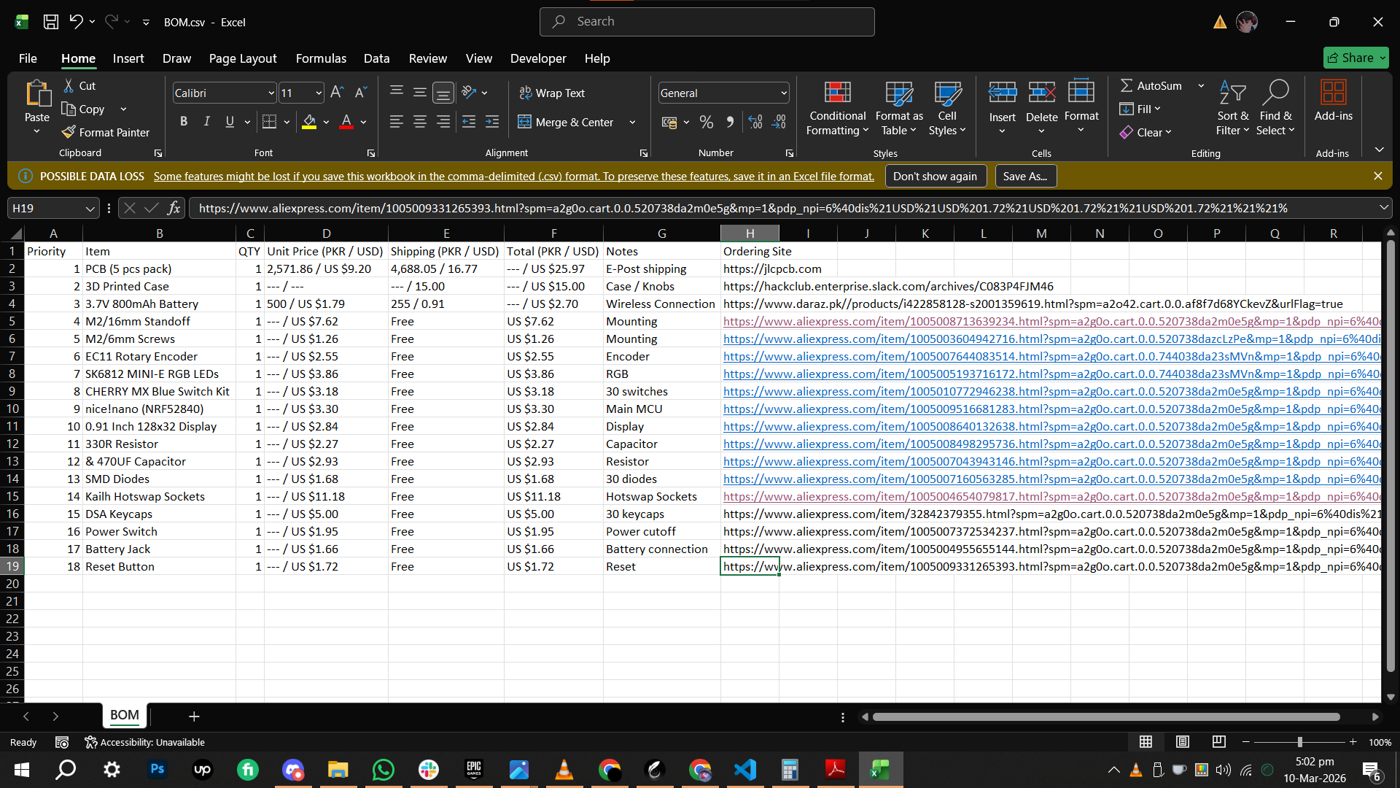
Images/BOM/Screenshot 2026-03-10 170257.png
