lassiipk/ModuPad_v2/Images/BOM/Screenshot 2026-03-16 203744.png

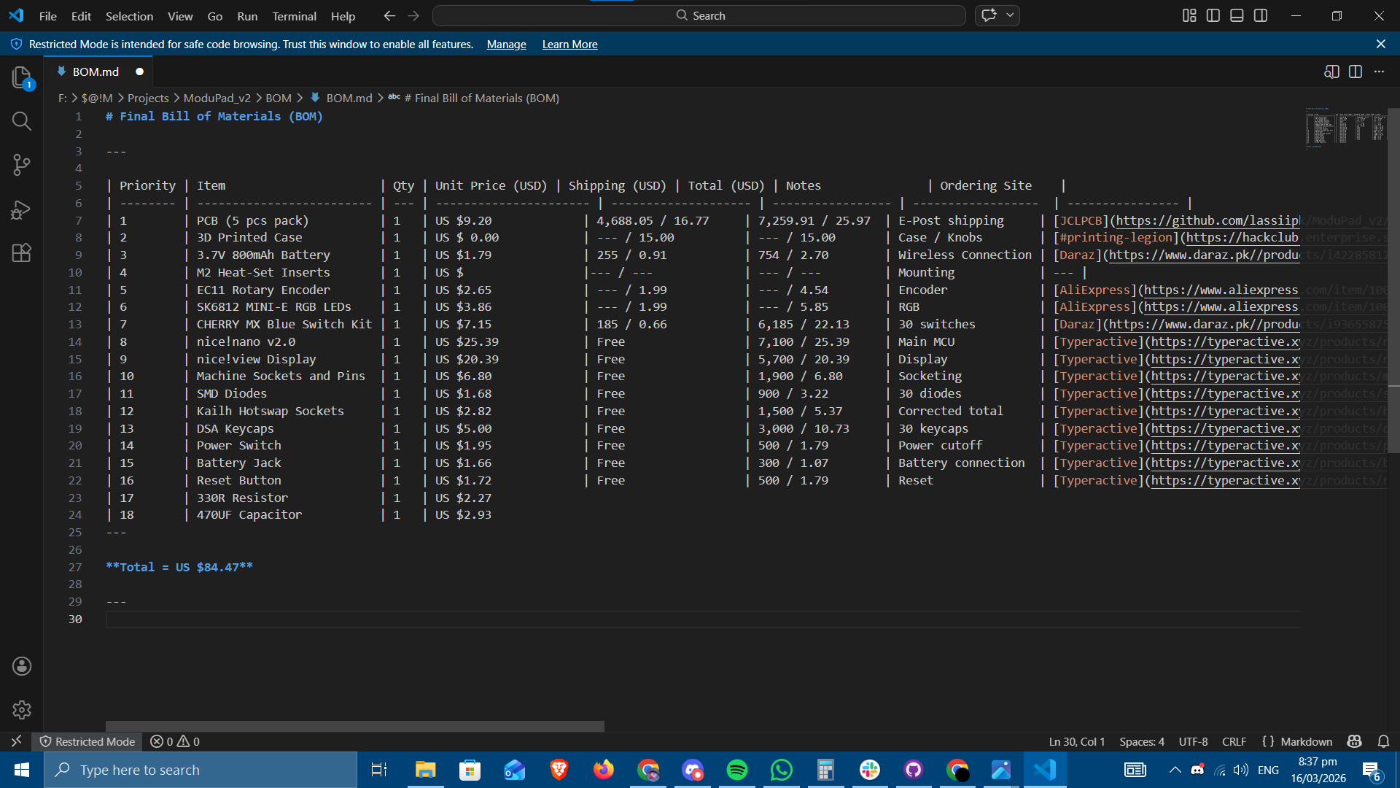
Images/BOM/Screenshot 2026-03-16 203744.png
