lassiipk/ModuPad_v2/Images/BOM/Screenshot 2026-03-19 090119.png

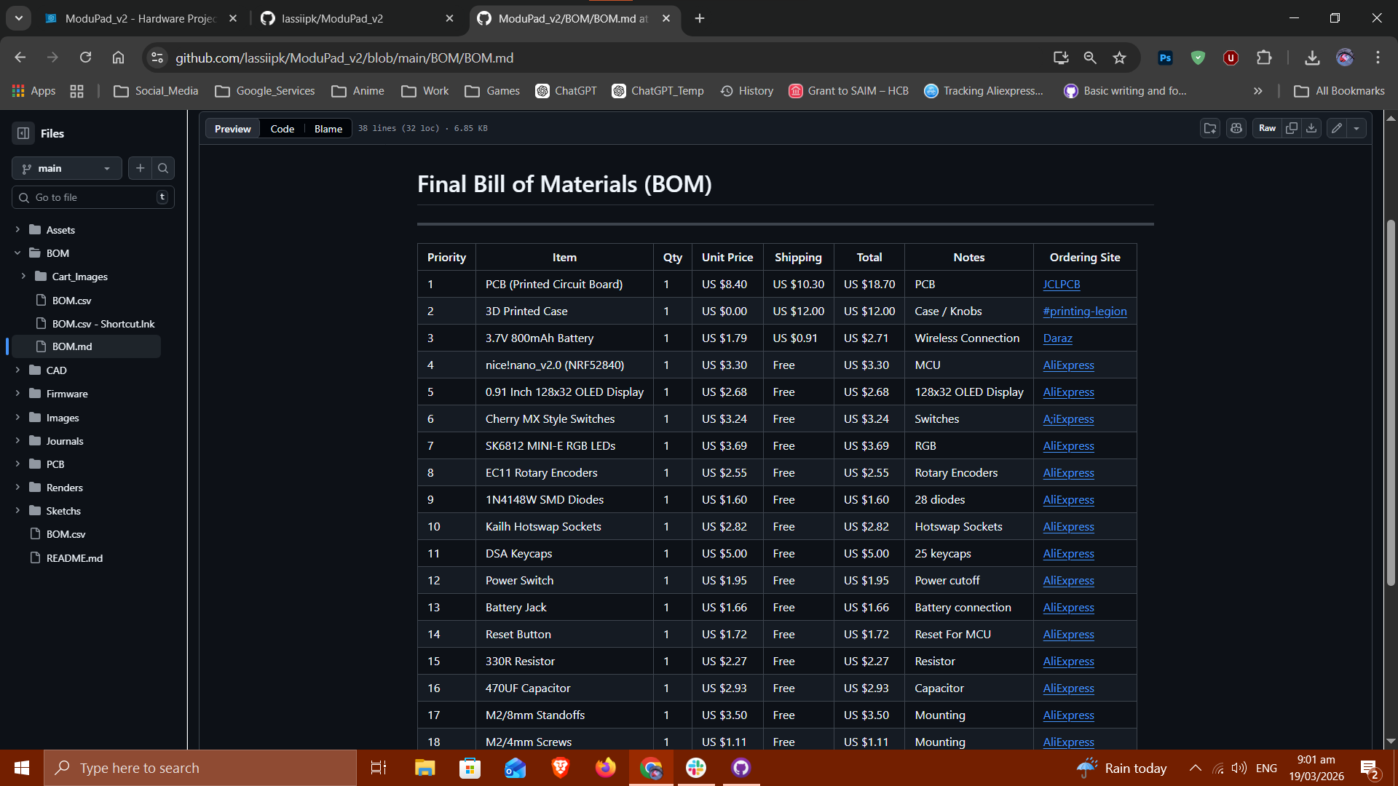
Images/BOM/Screenshot 2026-03-19 090119.png
