lassiipk/ModuPad_v2/CAD/Knobs/Knurled Encoder Knob/EncoderKnob.step

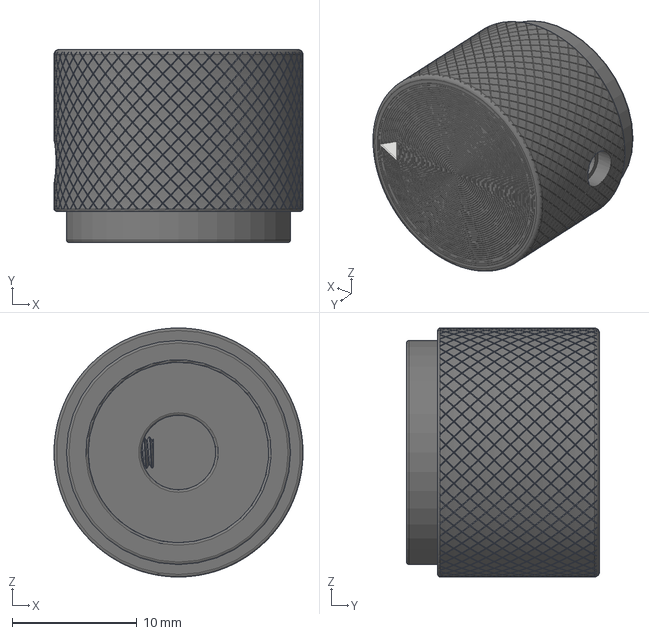
[picture p56: CAD file, 2026-02-17]
CAD/Knobs/Knurled Encoder Knob/EncoderKnob.step
20.0 x 15.5 x 20.0 mm
