lassiipk/ModuPad_v2/PCB/KiCad_FootPrints-3D-Models/nice!view/5-Pin-Header/5-Pin Header - Male - 2.54mm.step

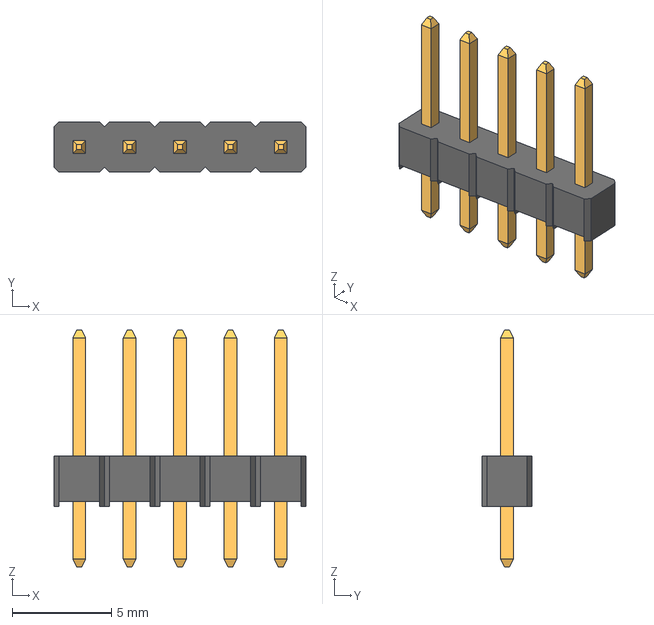
[picture p68: CAD file, 2026-02-14]
PCB/KiCad_FootPrints-3D-Models/nice!view/5-Pin-Header/5-Pin Header - Male - 2.54mm.step
12.7 x 2.54 x 11.9 mm
