lassiipk/ModuPad_v2/PCB/KiCad_FootPrints-3D-Models/nice!view/Display-Cover/typeractive-Model/Only-Cover/Only-Cover-Stl-Left.stl

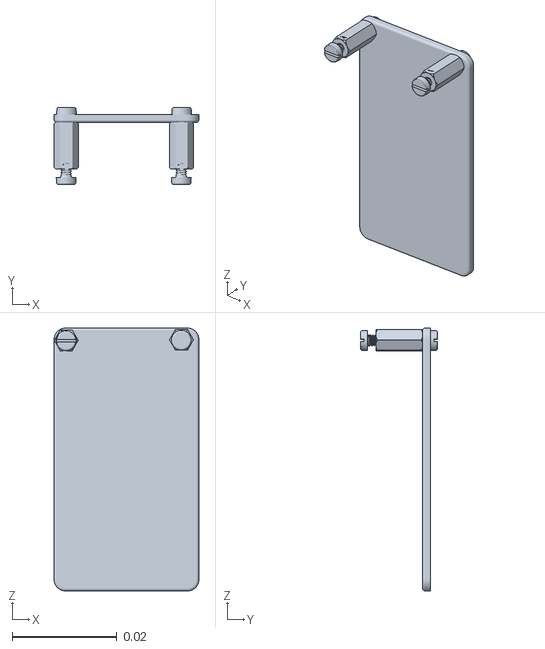
[picture p69: CAD file, 2026-02-14]
PCB/KiCad_FootPrints-3D-Models/nice!view/Display-Cover/typeractive-Model/Only-Cover/Only-Cover-Stl-Left.stl
0.0277 x 0.0147 x 0.0503
