lassiipk/ModuPad_v2/PCB/KiCad_FootPrints-3D-Models/nice!view/Display-Cover/typeractive-Model/Typeractive-Model_nice!nano-nice!view-Cover/Left/nice!nano_nice!view_Cover-STL-Left.stl

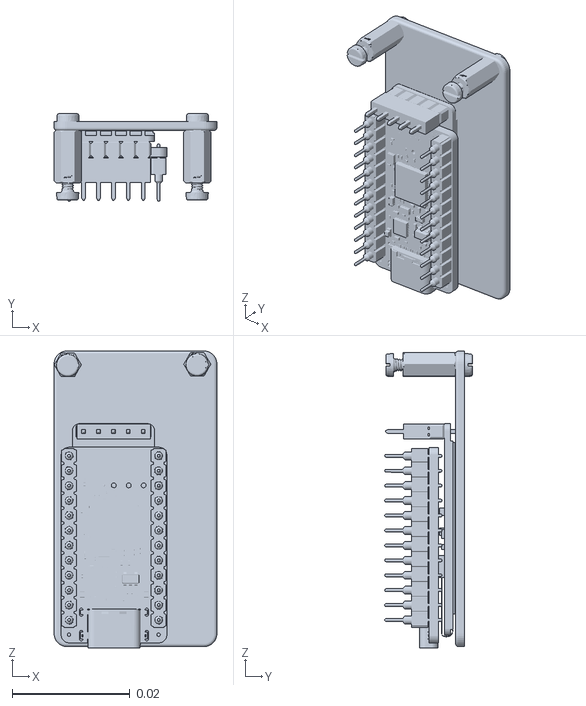
[picture p70: CAD file, 2026-02-14]
PCB/KiCad_FootPrints-3D-Models/nice!view/Display-Cover/typeractive-Model/Typeractive-Model_nice!nano-nice!view-Cover/Left/nice!nano_nice!view_Cover-STL-Left.stl
0.0277 x 0.0149 x 0.0505
