lassiipk/ModuPad_v2/PCB/KiCad_FootPrints-3D-Models/nice!view/nice!view/nice!view.step

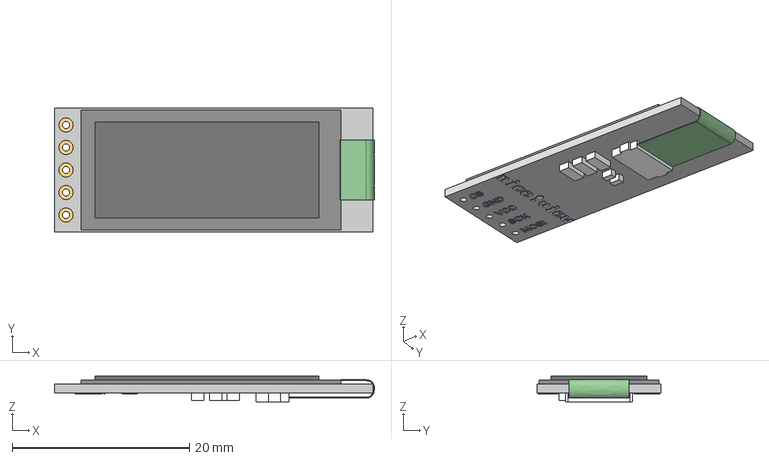
[picture p71: CAD file, 2026-02-14]
PCB/KiCad_FootPrints-3D-Models/nice!view/nice!view/nice!view.step
36.1 x 14.0 x 2.90 mm
