lassiipk/ModuPad_v2/PCB/KiCad_FootPrints-3D-Models/OLED_128x32/OLED_128x32.step

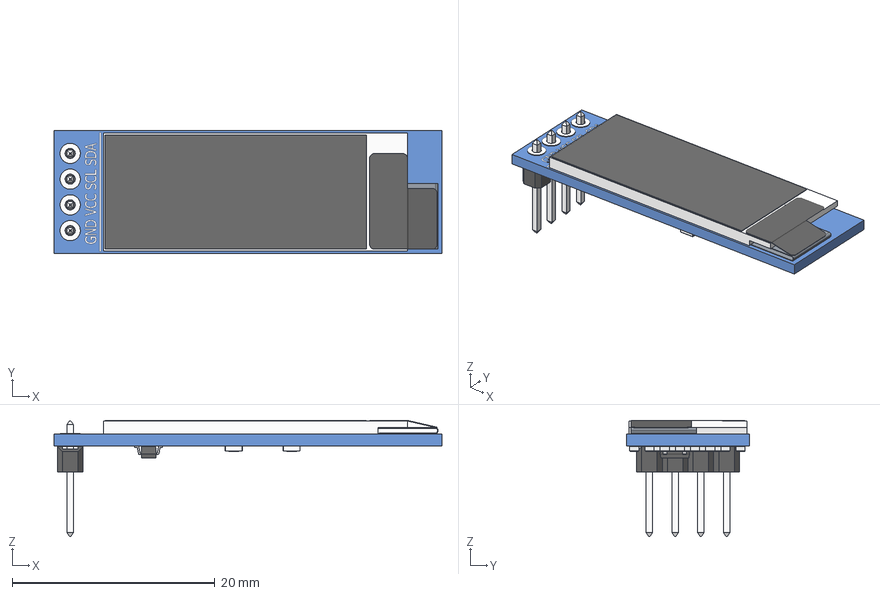
[picture p72: CAD file, 2026-03-10]
PCB/KiCad_FootPrints-3D-Models/OLED_128x32/OLED_128x32.step
38.3 x 12.1 x 11.5 mm
OLED_0.91_128x32
Pin Header 4 x 1 TH 2.54mm Pitch
RESC-0603 x 13
2SD0601A
