lassiipk/ModuPad_v2/PCB/KiCad_FootPrints-3D-Models/Power Switch_{1.4(H)mm, 1.52.0mm-travel Surface Mount Type SSSS811101}/SSSS811101--3DModel-STEP-269445.STEP

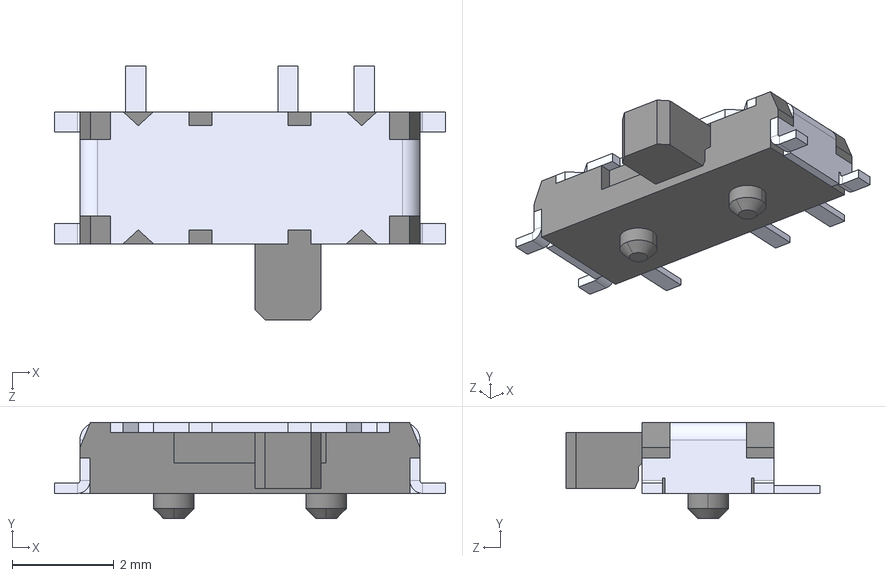
[picture p73: CAD file, 2026-02-14]
PCB/KiCad_FootPrints-3D-Models/Power Switch_{1.4(H)mm, 1.52.0mm-travel Surface Mount Type SSSS811101}/SSSS811101--3DModel-STEP-269445.STEP
7.70 x 1.90 x 5.00 mm
