lassiipk/ModuPad_v2/PCB/KiCad_FootPrints-3D-Models/SK6812MINI-E/SK6812-E--3DModel-STEP-418109.STEP

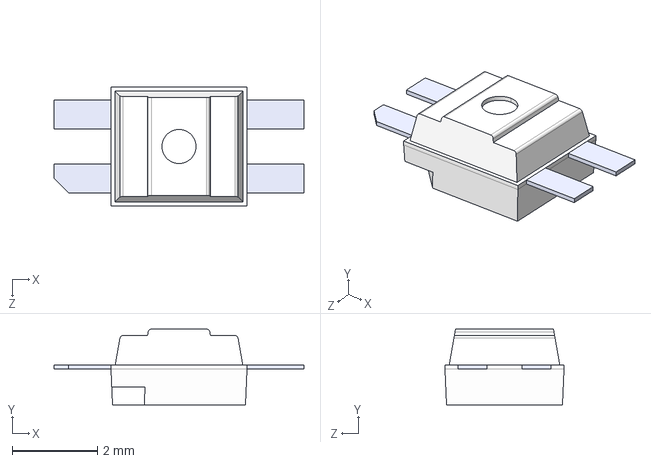
[picture p74: CAD file, 2026-02-14]
PCB/KiCad_FootPrints-3D-Models/SK6812MINI-E/SK6812-E--3DModel-STEP-418109.STEP
5.88 x 1.78 x 2.80 mm
