lassiipk/ModuPad_v2/PCB/KiCad_FootPrints/Capacitor/478CKS010M.step

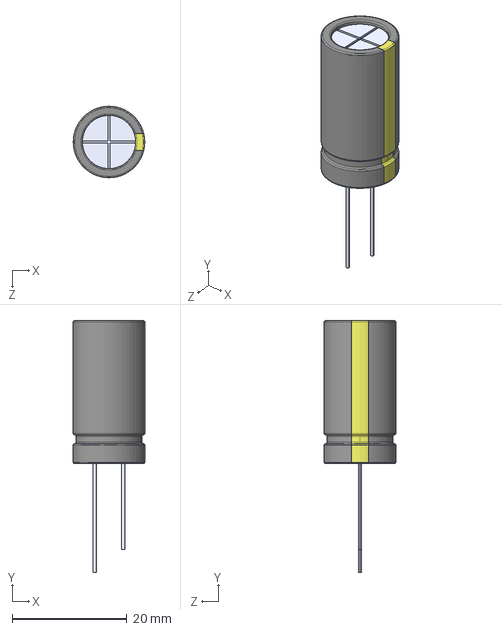
[picture p75: CAD file, 2026-03-10]
PCB/KiCad_FootPrints/Capacitor/478CKS010M.step
12.5 x 44.0 x 12.5 mm
