lassiipk/ModuPad_v2/PCB/KiCad_FootPrints/Resistor/MFR-25FBF52-1K.step

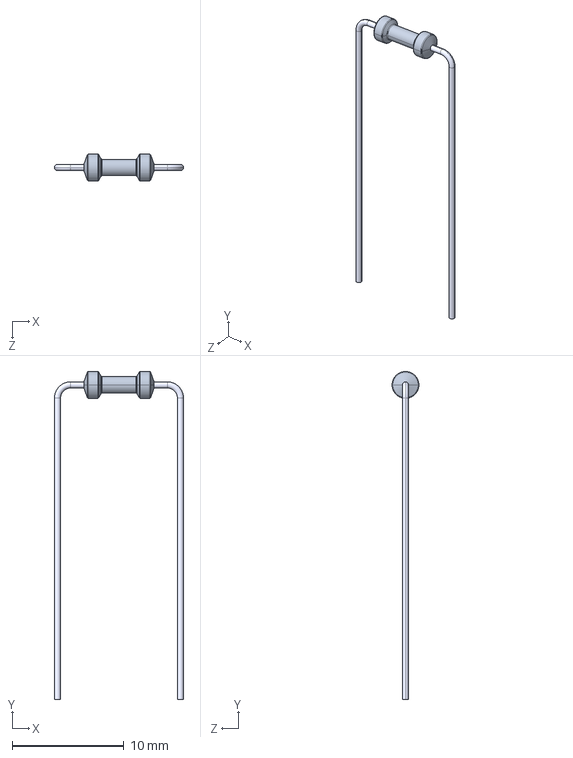
[picture p76: CAD file, 2026-03-10]
PCB/KiCad_FootPrints/Resistor/MFR-25FBF52-1K.step
11.5 x 29.4 x 2.40 mm
