lassiipk/ModuPad_v2/PCB/KiCad_FootPrints-3D-Models/nice!nano-v2/12-Pin-Header/12-Pin Header - Male - 2.54mm.step

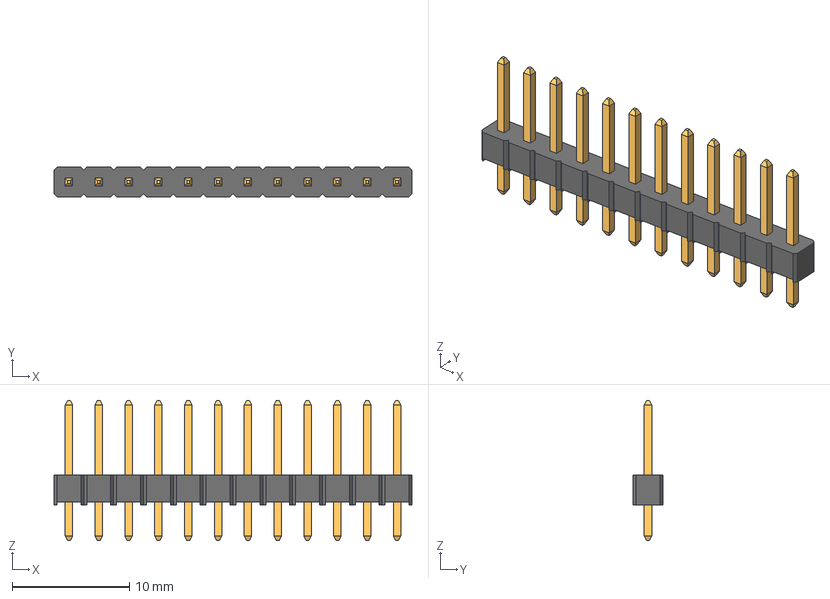
[picture p77: CAD file, 2026-02-14]
PCB/KiCad_FootPrints-3D-Models/nice!nano-v2/12-Pin-Header/12-Pin Header - Male - 2.54mm.step
30.5 x 2.54 x 11.9 mm
