lassiipk/ModuPad_v2/PCB/KiCad_FootPrints-3D-Models/nice!nano-v2/3-Pin-Header/Female 3 Pin Header.step

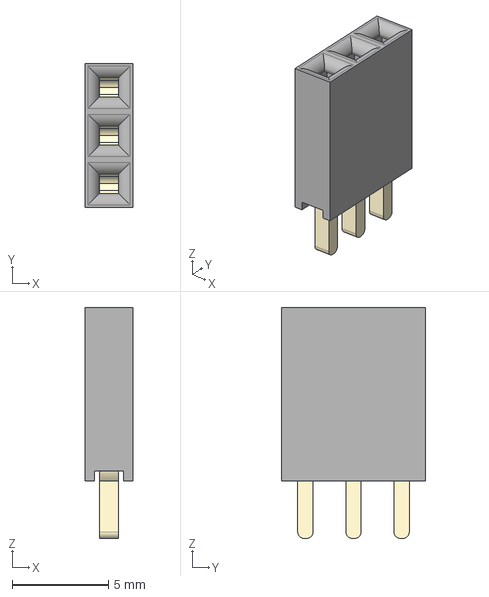
[picture p78: CAD file, 2026-02-14]
PCB/KiCad_FootPrints-3D-Models/nice!nano-v2/3-Pin-Header/Female 3 Pin Header.step
2.50 x 7.50 x 12.0 mm
