lassiipk/ModuPad_v2/PCB/KiCad_FootPrints-3D-Models/nice!view/5-Pin-Header/Female 5 Pin Header.step

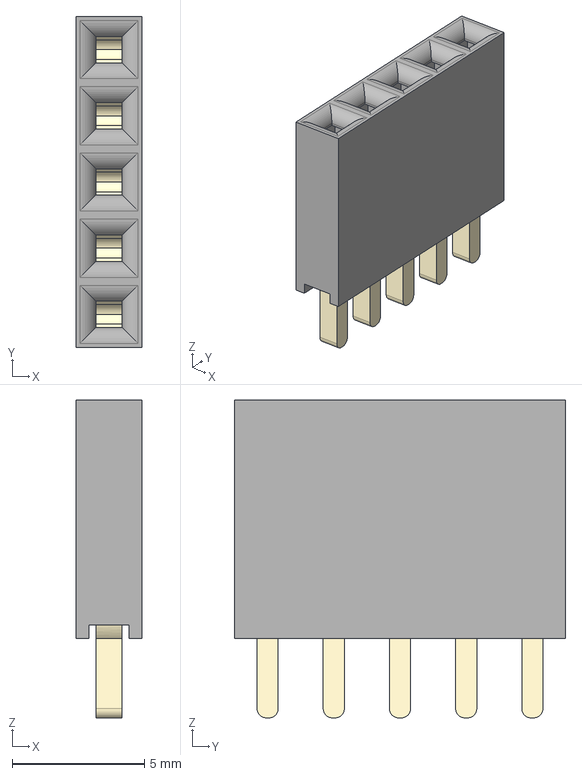
[picture p79: CAD file, 2026-02-14]
PCB/KiCad_FootPrints-3D-Models/nice!view/5-Pin-Header/Female 5 Pin Header.step
2.50 x 12.5 x 12.0 mm
