lassiipk/ModuPad_v2/CAD/Upper-Plate/.DXF/ai03 Plate Generator_5x5 Keys.dxf

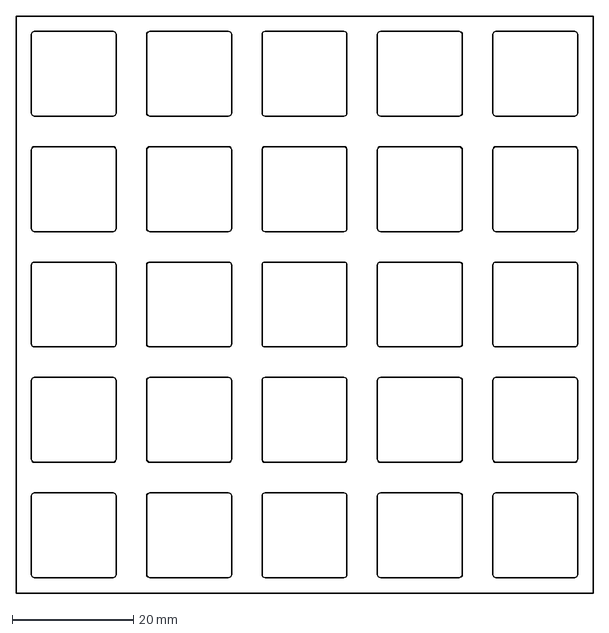
[picture p80: CAD file, 2026-02-14]
CAD/Upper-Plate/.DXF/ai03 Plate Generator_5x5 Keys.dxf
95.2 x 95.2 mm
