lassiipk/ModuPad_v2/BOM/Cart_Images/#printing-legion_Screenshot 2026-02-17 113534.png

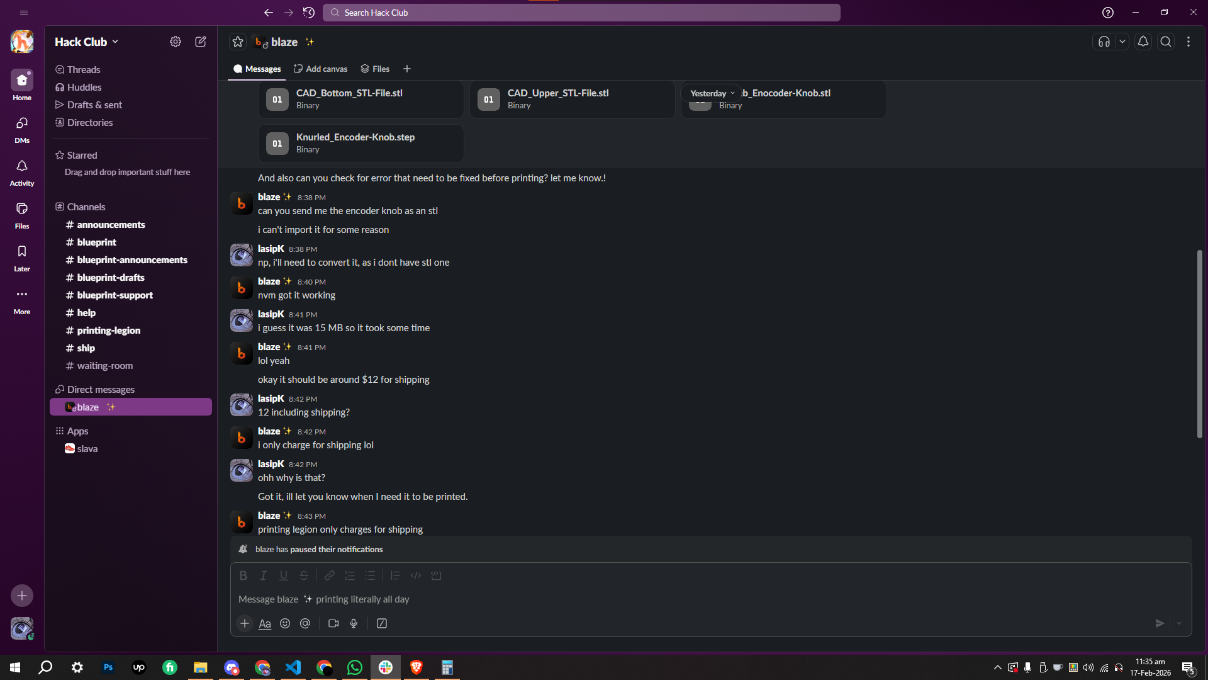
BOM/Cart_Images/#printing-legion_Screenshot 2026-02-17 113534.png
