lassiipk/ModuPad_v2/Sketchs/PNGs/New_Design/2.o___ModuPad_v2_Sketch-PNG-Dark-Mode_3xScale_PCB-Measurements.excalidraw.png

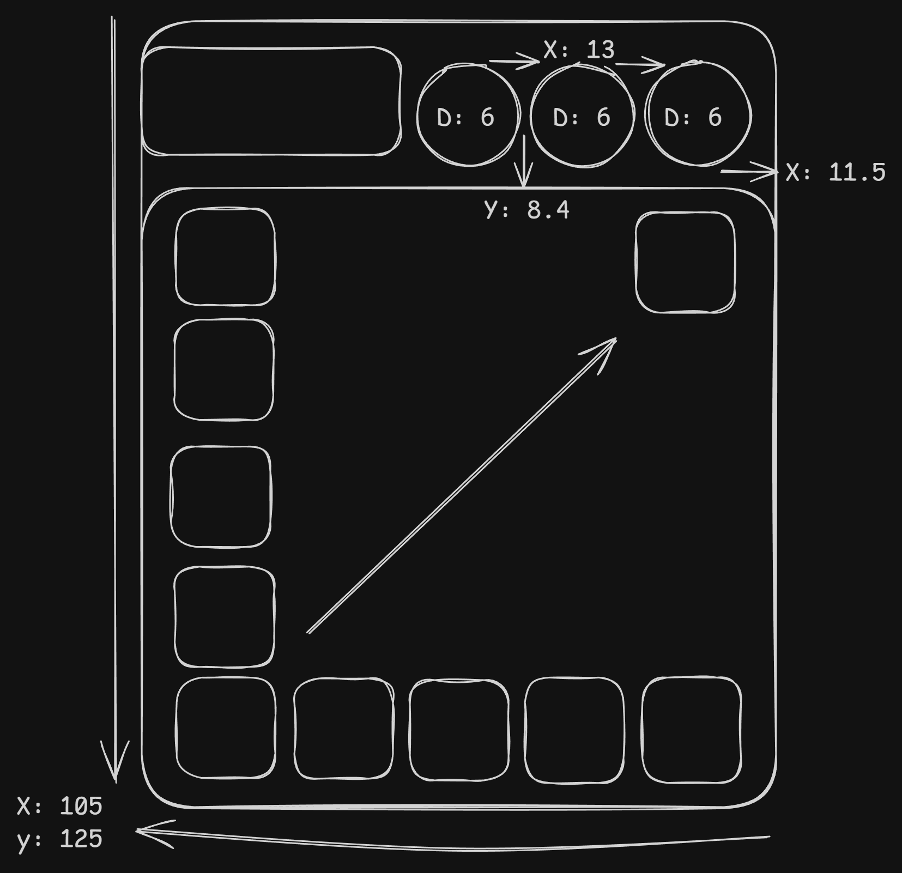
Sketchs/PNGs/New_Design/2.o___ModuPad_v2_Sketch-PNG-Dark-Mode_3xScale_PCB-Measurements.excalidraw.png
